mblunt/DETECTS2020/Pictures/0001-3077525328.png

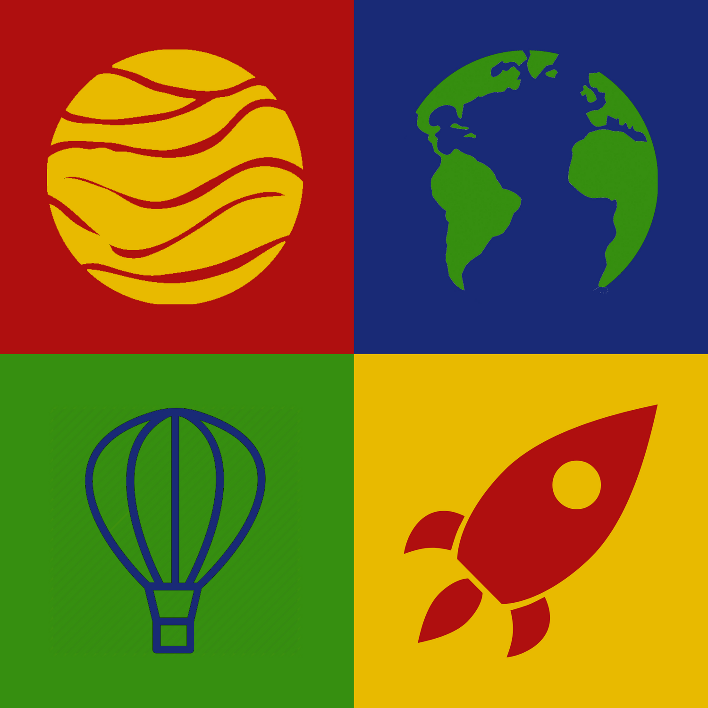
Pictures/0001-3077525328.png
