mblunt/DETECTS2020/Pictures/20191219_141400.jpg

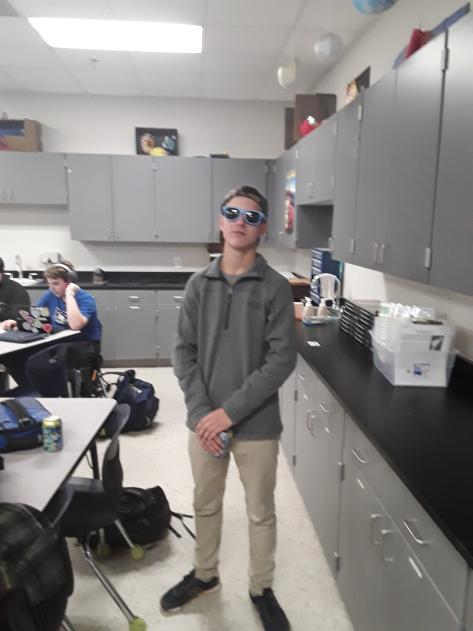
Pictures/20191219_141400.jpg
