mblunt/DETECTS2020/Pictures/After burn.jpg

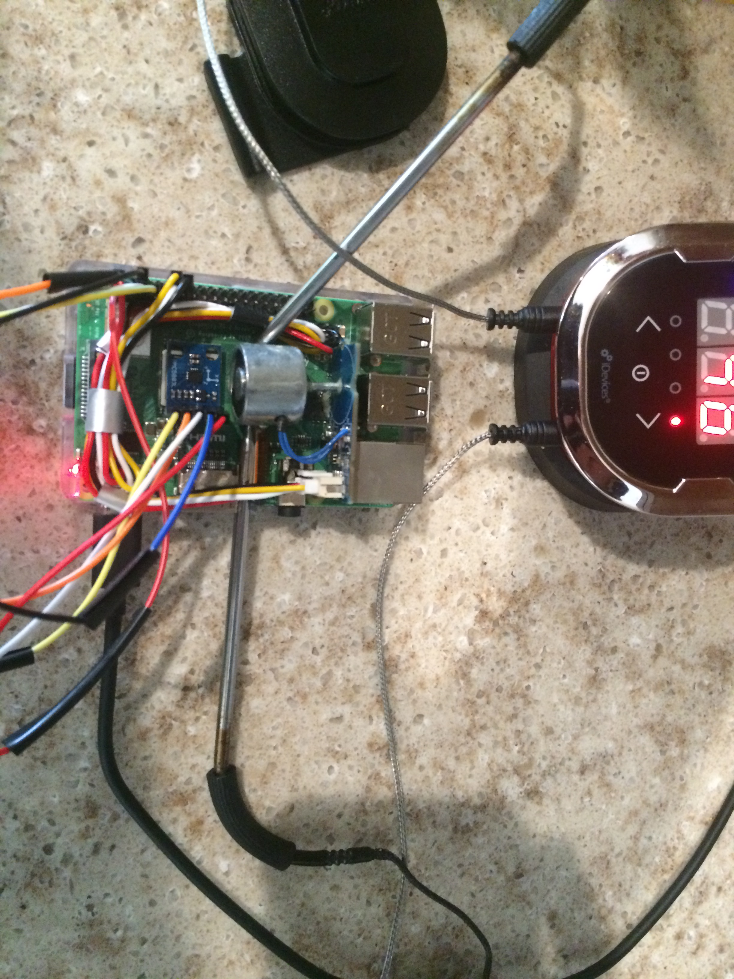
Pictures/After burn.jpg
