mblunt/DETECTS2020/Pictures/Burning PM.jpg

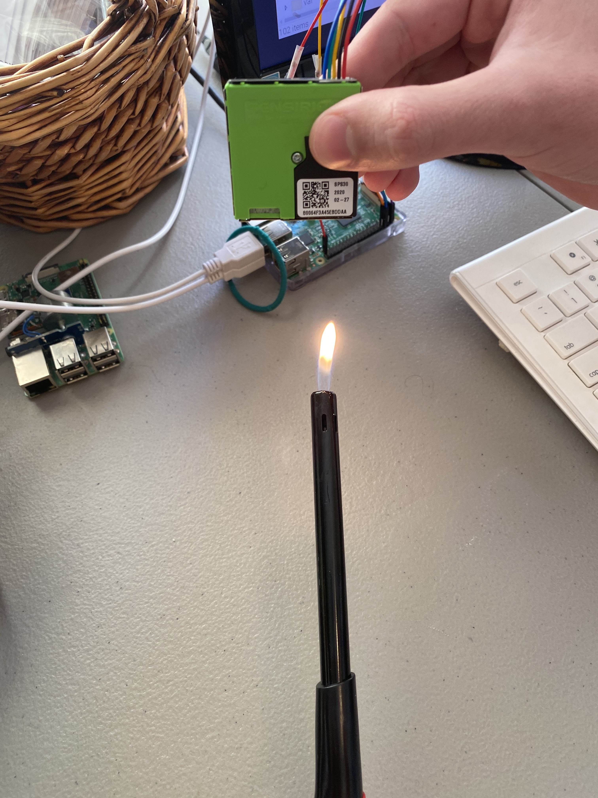
Pictures/Burning PM.jpg
