mblunt/DETECTS2020/Pictures/CAD_model.PNG

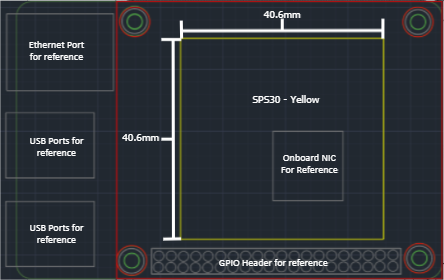
Pictures/CAD_model.PNG
