mblunt/DETECTS2020/Pictures/consistency_picture.PNG

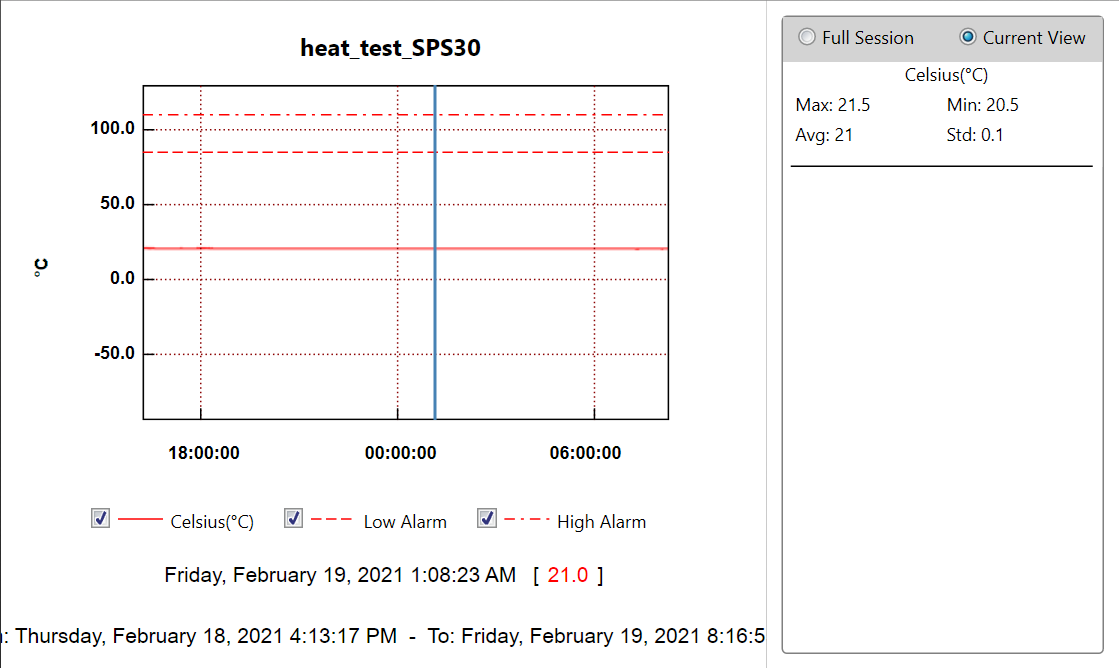
Pictures/consistency_picture.PNG
