mblunt/DETECTS2020/Pictures/datapacket.png

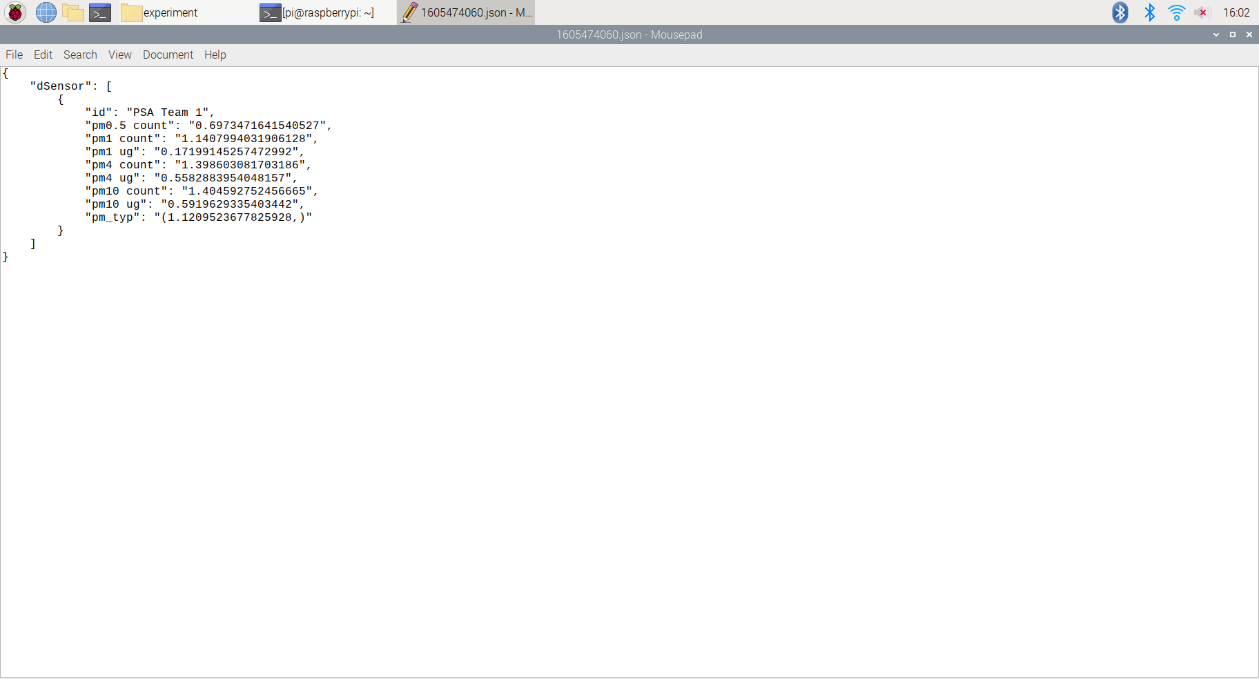
Pictures/datapacket.png
