mblunt/DETECTS2020/Pictures/datarate.png

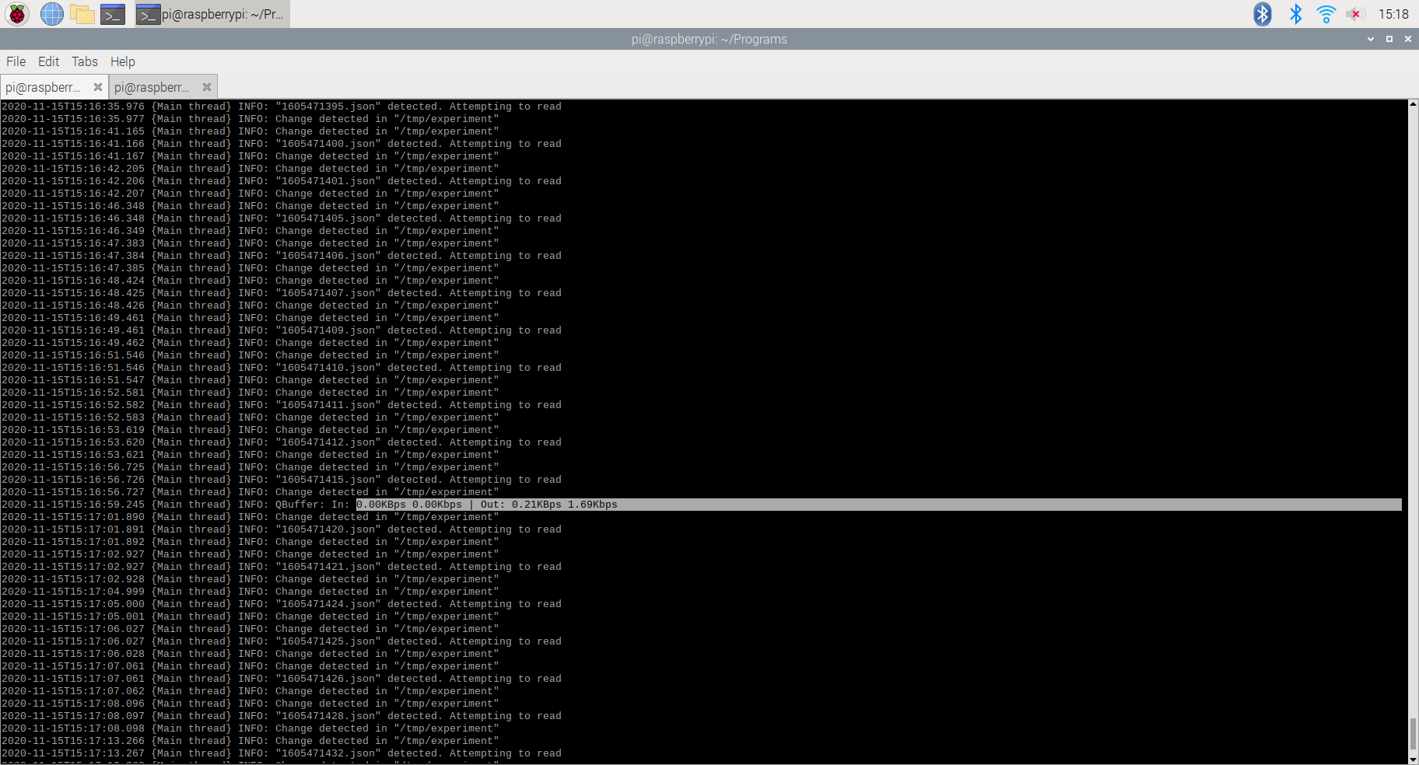
Pictures/datarate.png
