mblunt/DETECTS2020/Pictures/File_000(1).jpeg

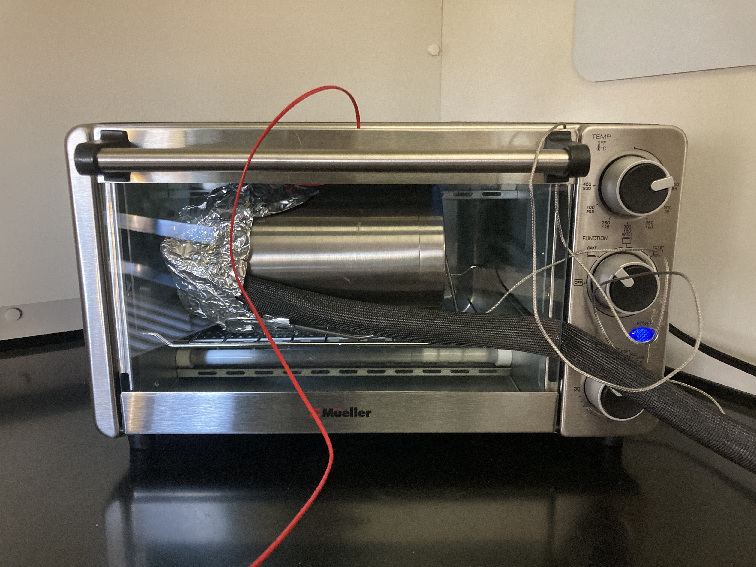
Pictures/File_000(1).jpeg
