mblunt/DETECTS2020/Pictures/File_000(5).jpeg

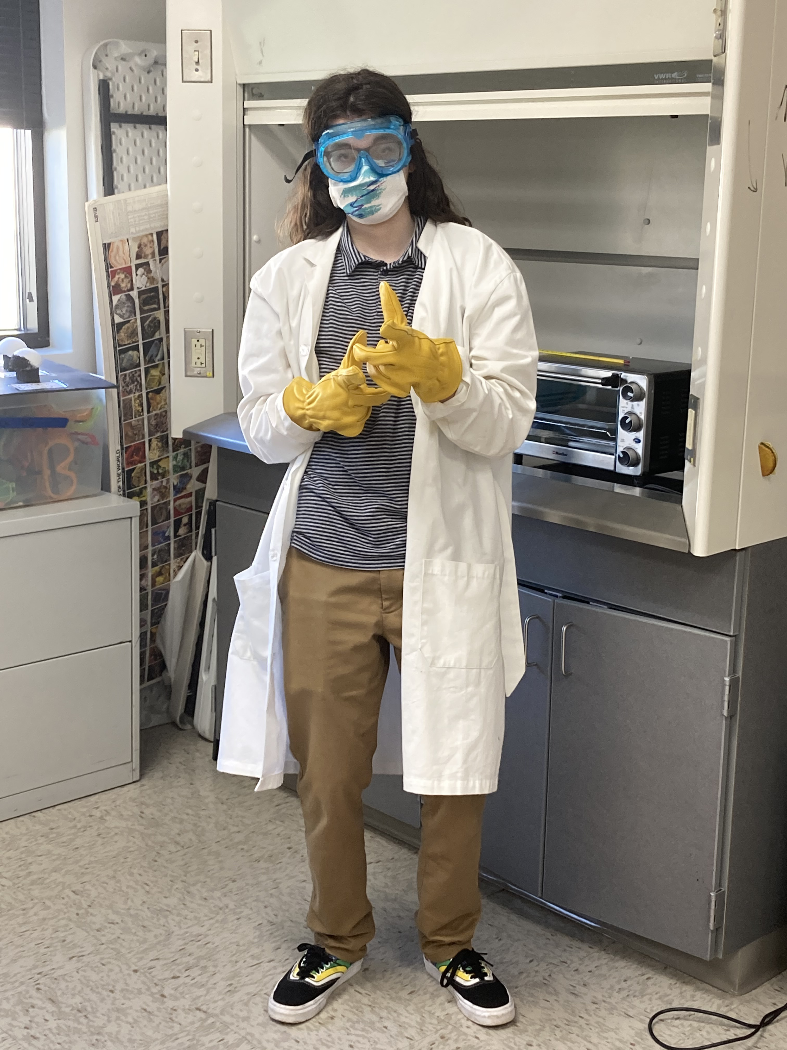
Pictures/File_000(5).jpeg
