mblunt/DETECTS2020/Pictures/File_000(6).jpeg

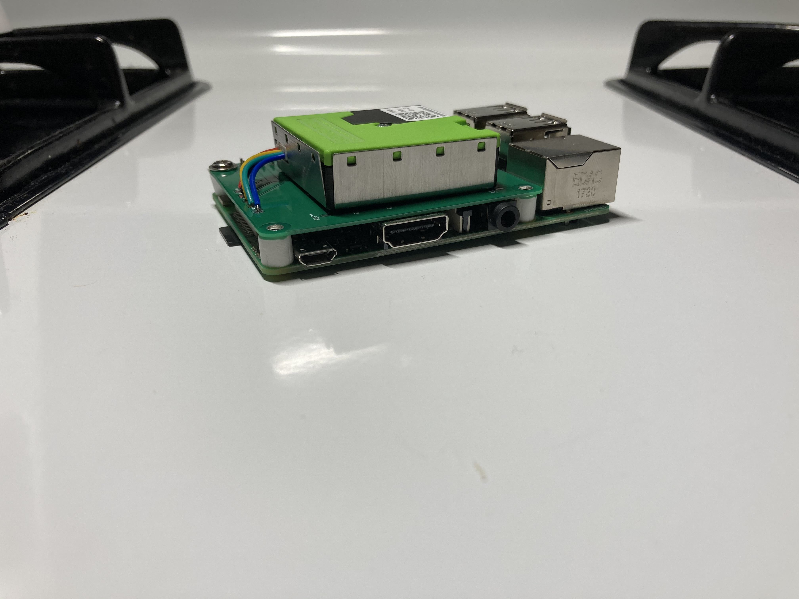
Pictures/File_000(6).jpeg
