mblunt/DETECTS2020/Pictures/File_000(7).jpeg

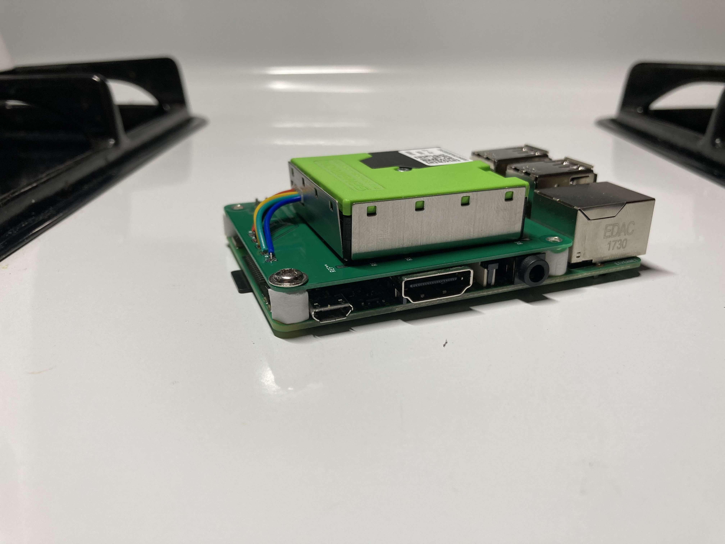
Pictures/File_000(7).jpeg
