mblunt/DETECTS2020/Pictures/File_000(8).jpeg

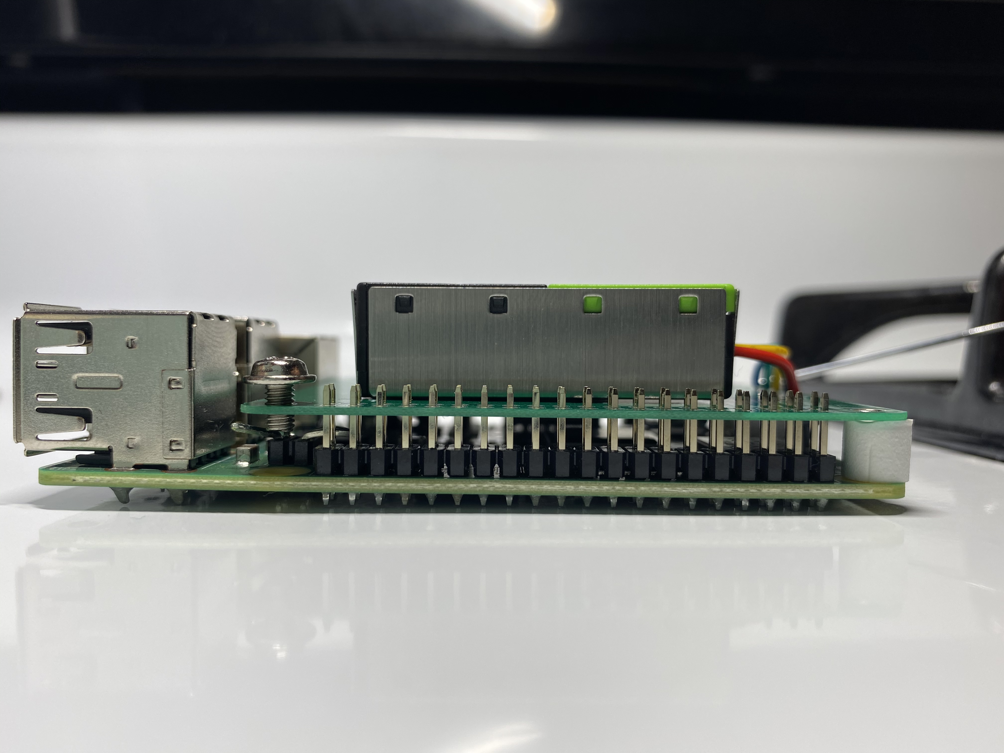
Pictures/File_000(8).jpeg
