mblunt/DETECTS2020/Pictures/File_000(9).jpeg

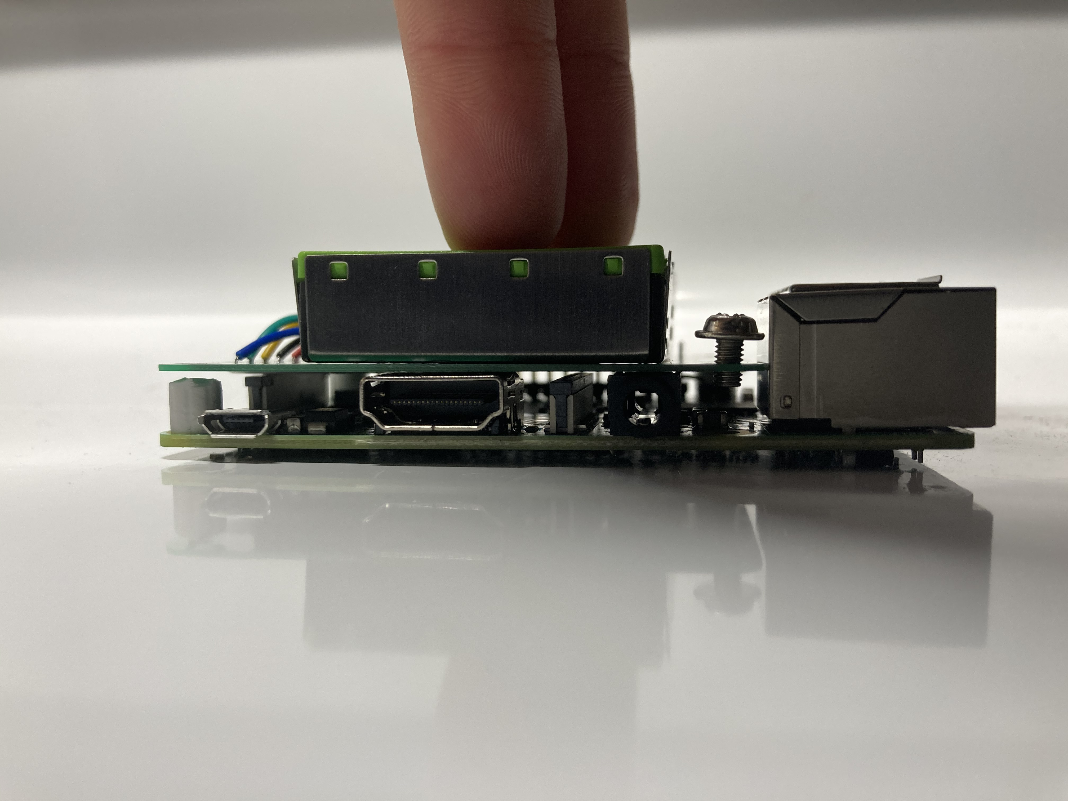
Pictures/File_000(9).jpeg
