mblunt/DETECTS2020/Pictures/File_000(10).jpeg

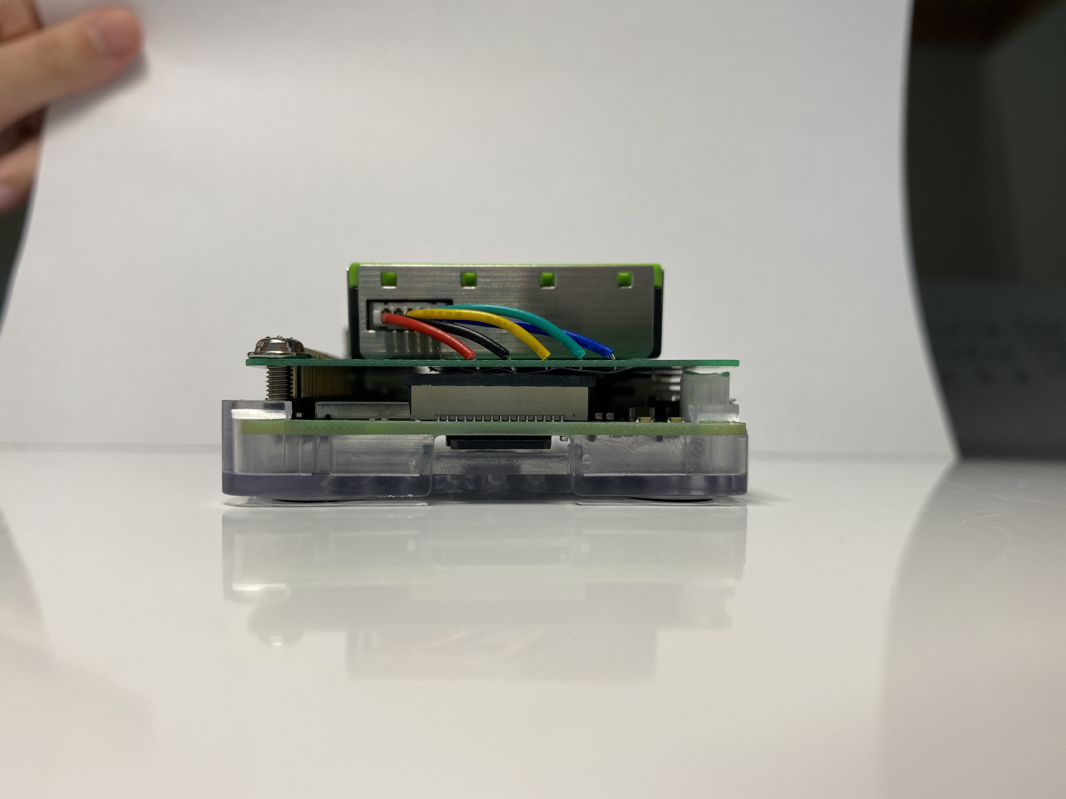
Pictures/File_000(10).jpeg
