mblunt/DETECTS2020/Pictures/File_000.jpeg

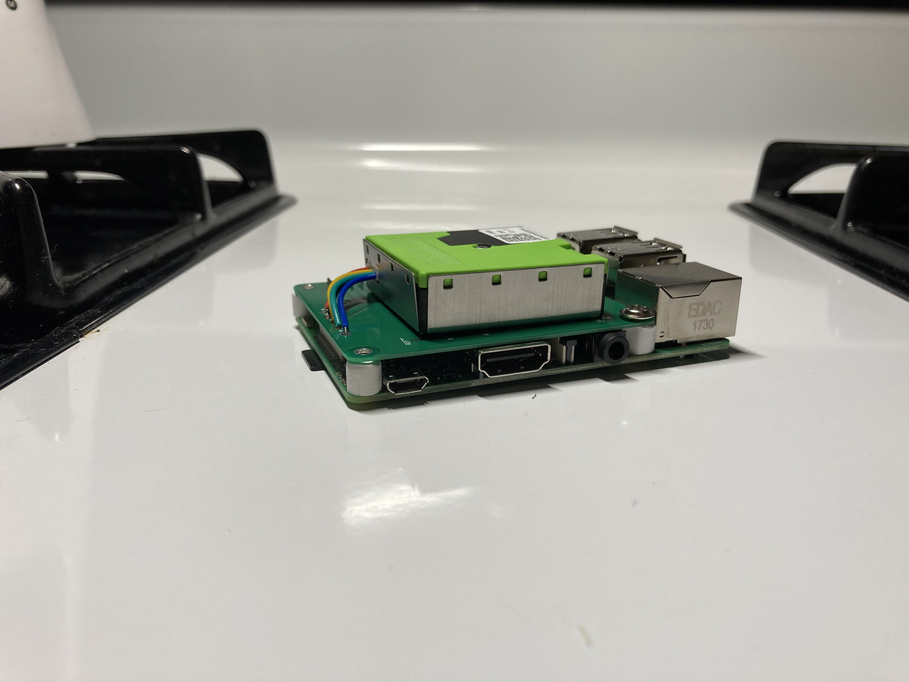
Pictures/File_000.jpeg
