mblunt/DETECTS2020/Pictures/File_001(2).jpeg

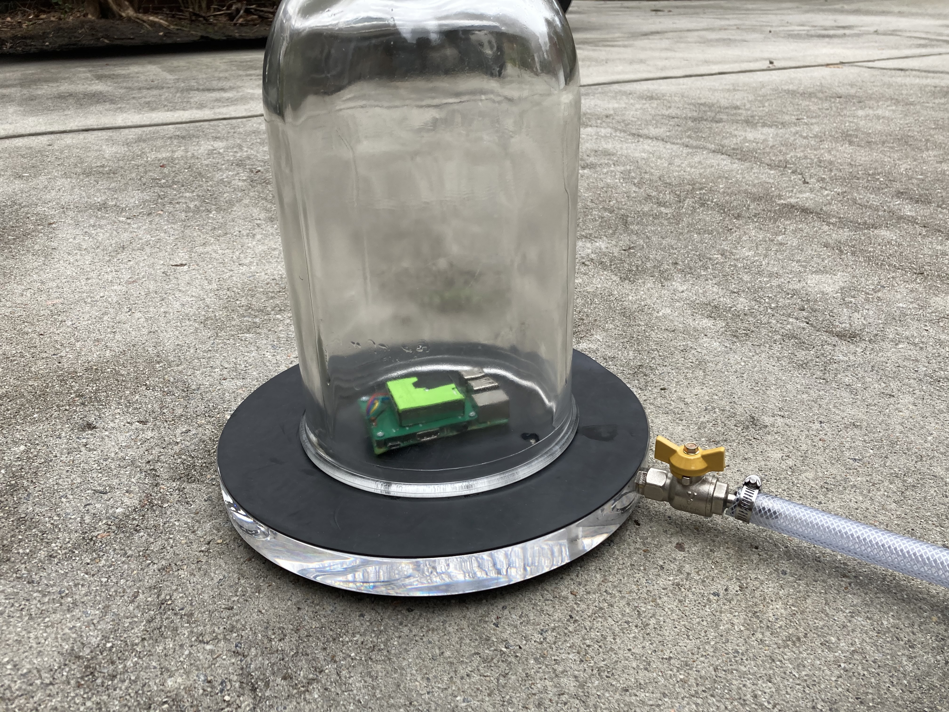
Pictures/File_001(2).jpeg
