mblunt/DETECTS2020/Pictures/File_001(3).jpeg

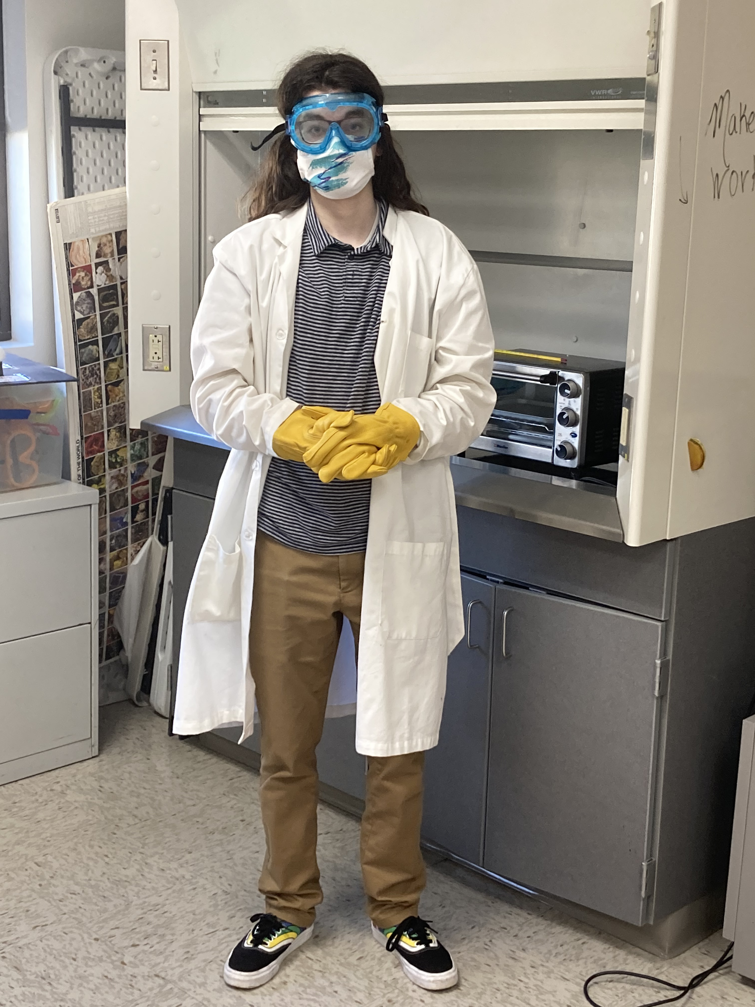
Pictures/File_001(3).jpeg
