mblunt/DETECTS2020/Pictures/File_001(6).jpeg

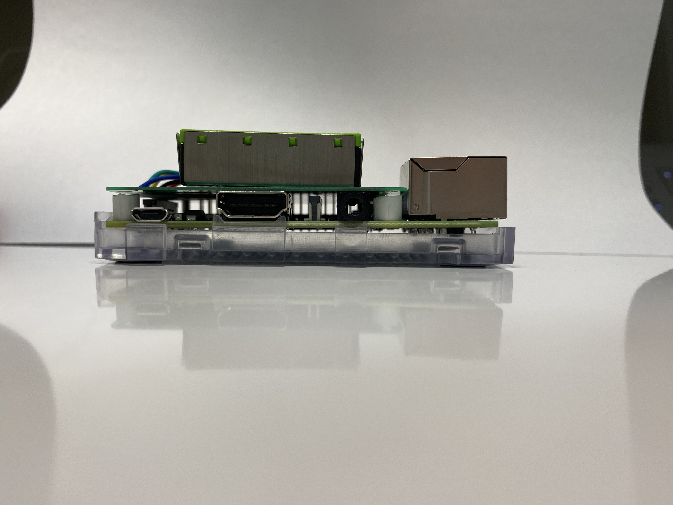
Pictures/File_001(6).jpeg
