mblunt/DETECTS2020/Pictures/File_001.jpeg

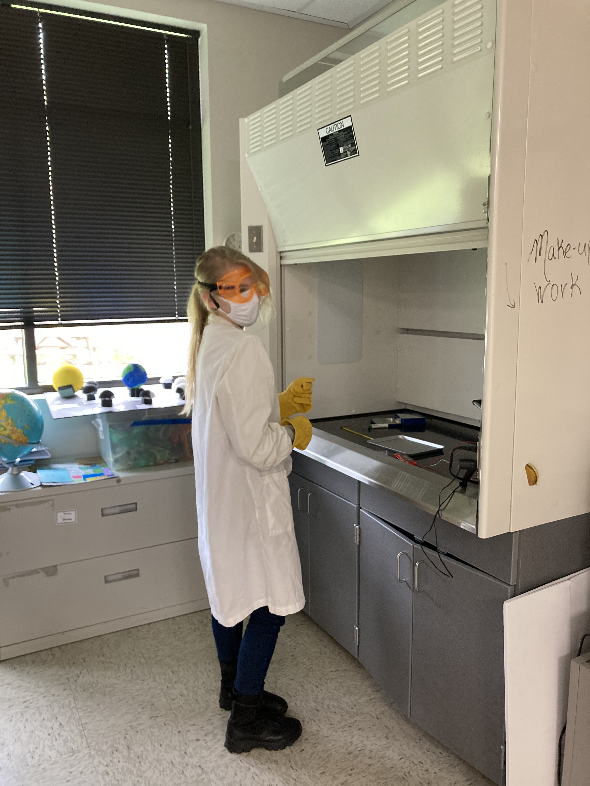
Pictures/File_001.jpeg
