mblunt/DETECTS2020/Pictures/File_002(1).jpeg

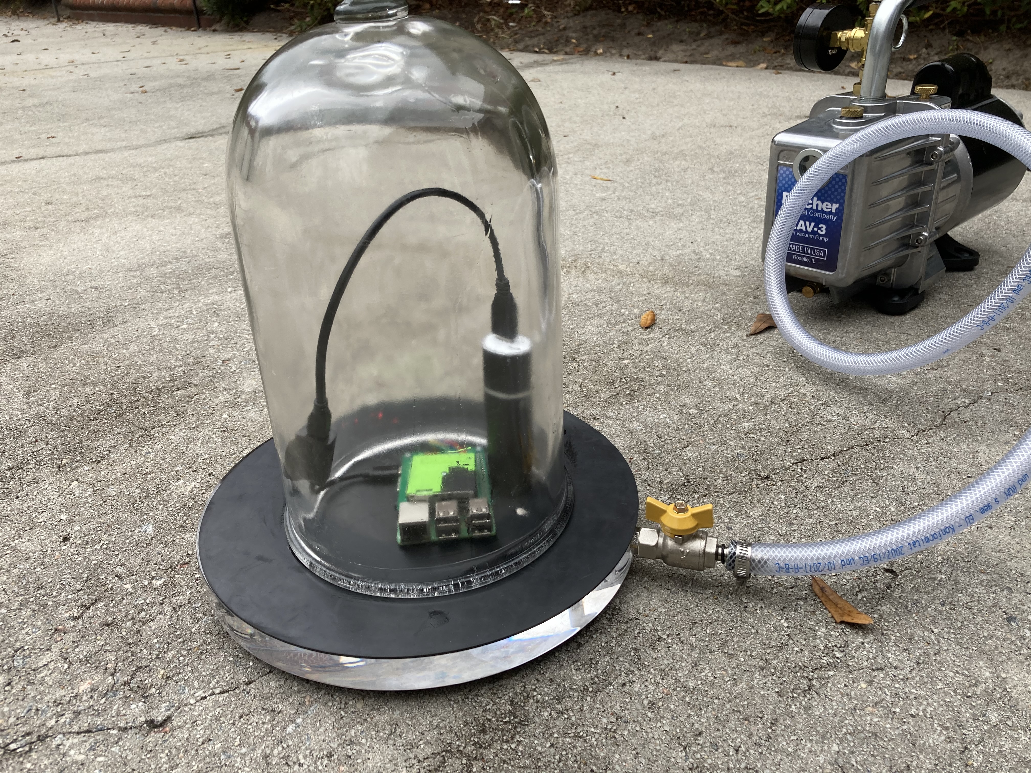
Pictures/File_002(1).jpeg
