mblunt/DETECTS2020/Pictures/File_002(2).jpeg

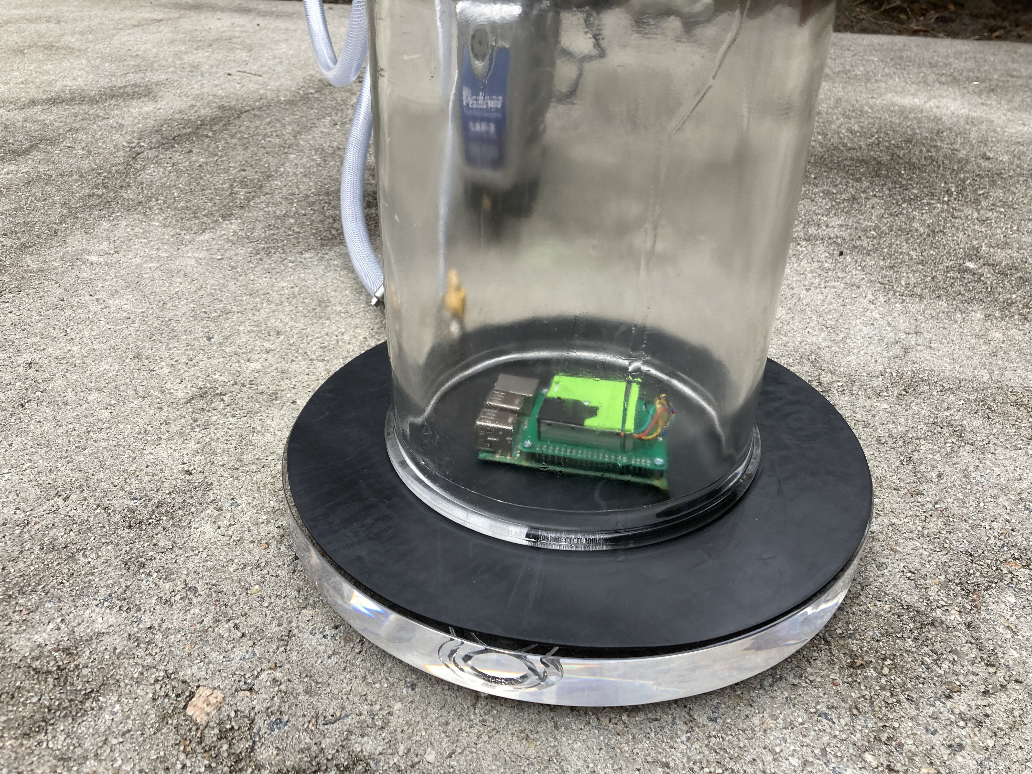
Pictures/File_002(2).jpeg
