mblunt/DETECTS2020/Pictures/File_002(3).jpeg

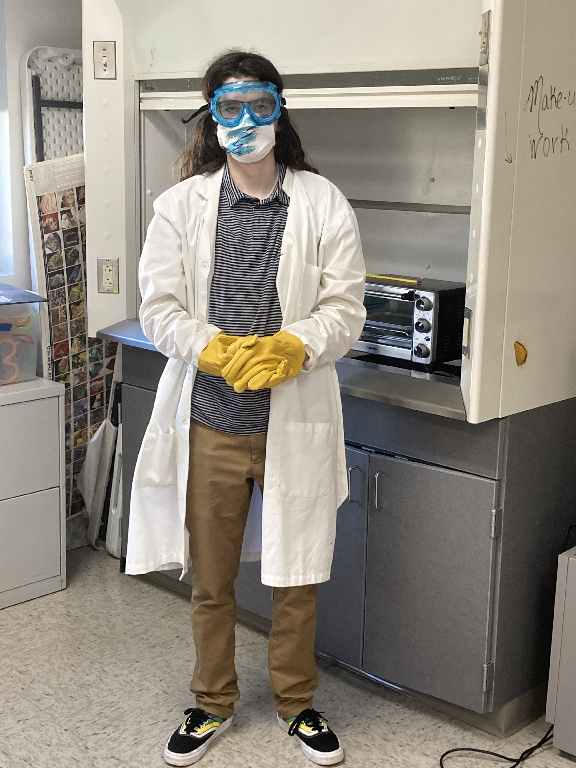
Pictures/File_002(3).jpeg
