mblunt/DETECTS2020/Pictures/File_002(4).jpeg

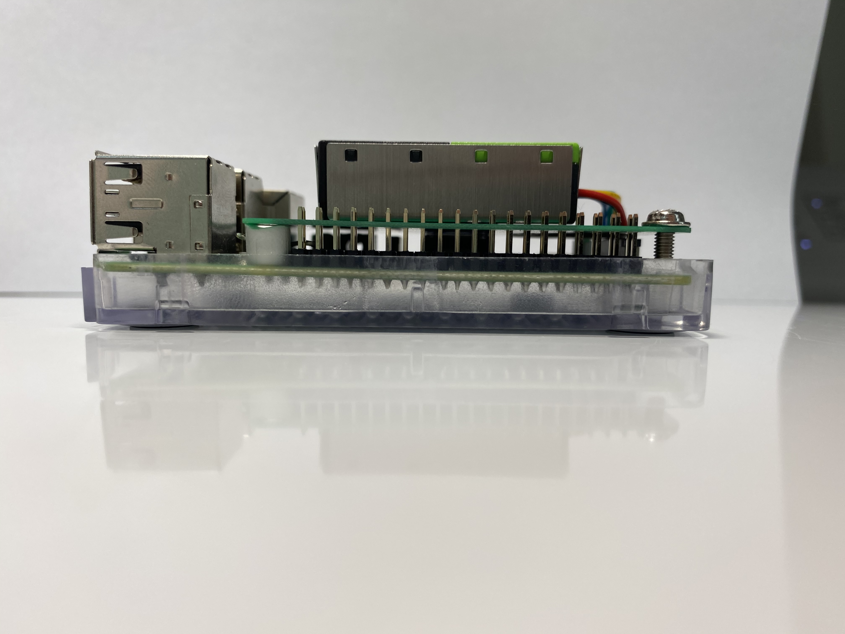
Pictures/File_002(4).jpeg
