mblunt/DETECTS2020/Pictures/File_002.jpeg

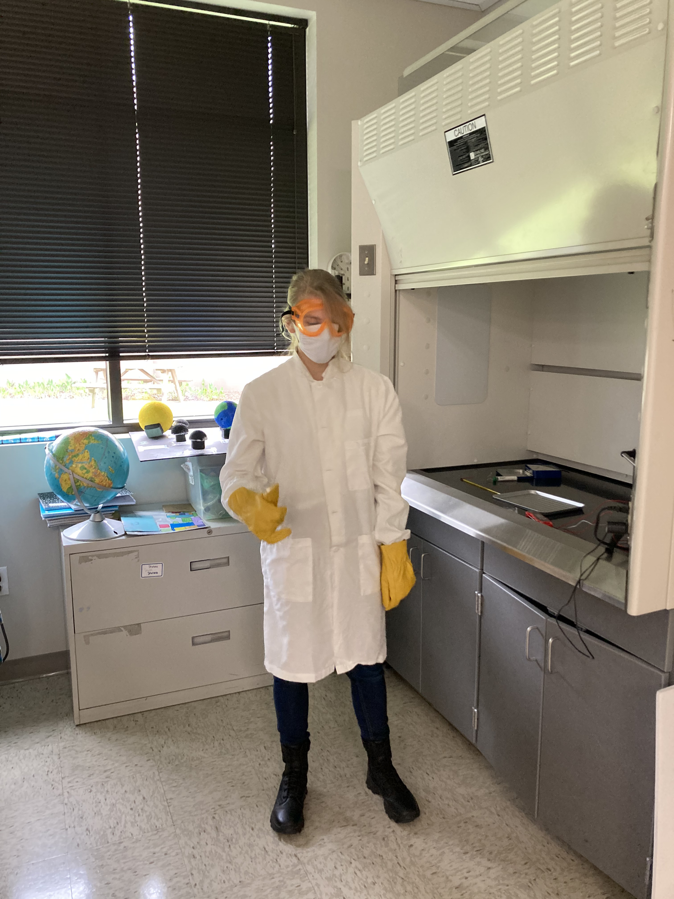
Pictures/File_002.jpeg
