mblunt/DETECTS2020/Pictures/File_003(1).jpeg

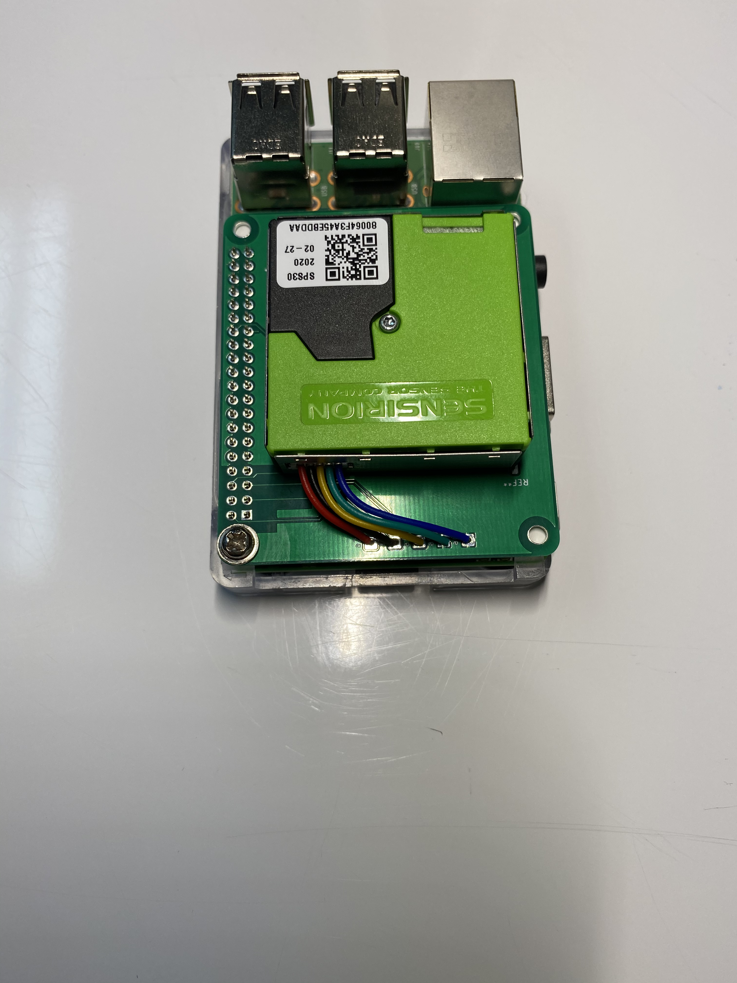
Pictures/File_003(1).jpeg
