mblunt/DETECTS2020/Pictures/File_003(2).jpeg

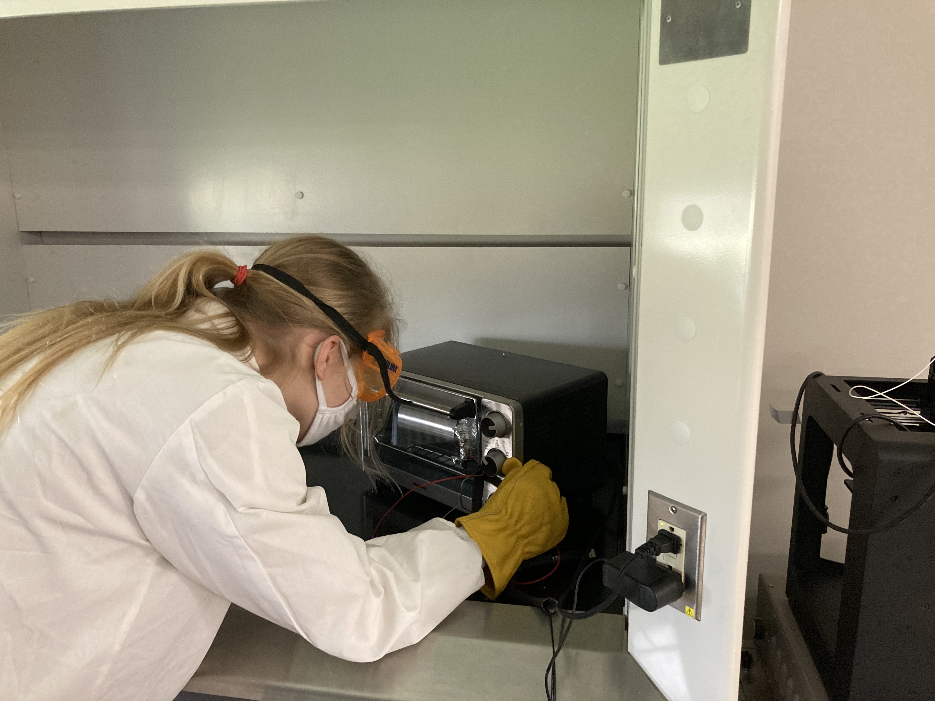
Pictures/File_003(2).jpeg
