mblunt/DETECTS2020/Pictures/File_003(3).jpeg

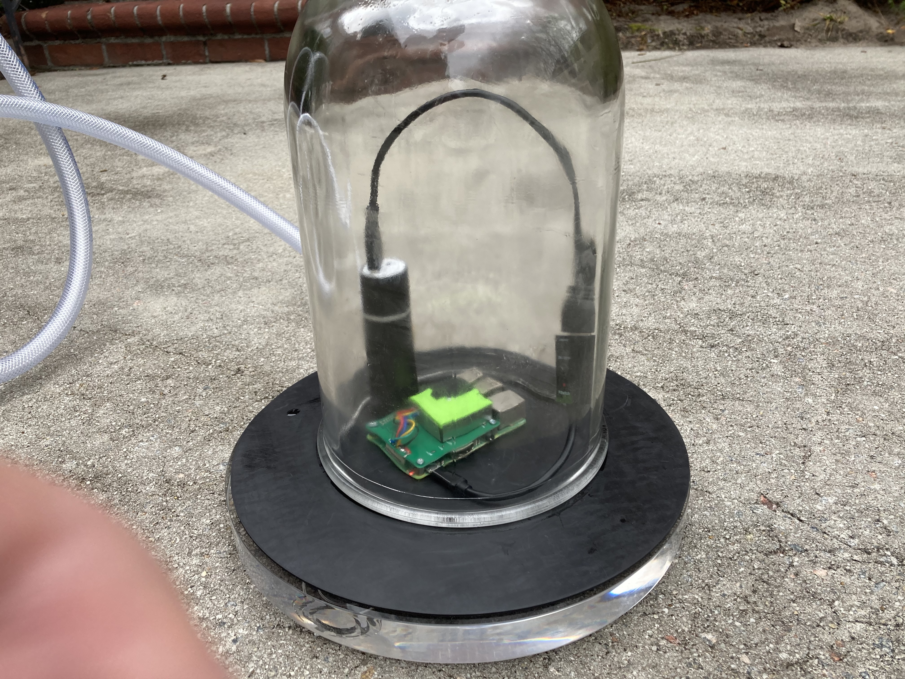
Pictures/File_003(3).jpeg
