mblunt/DETECTS2020/Pictures/File_003.jpeg

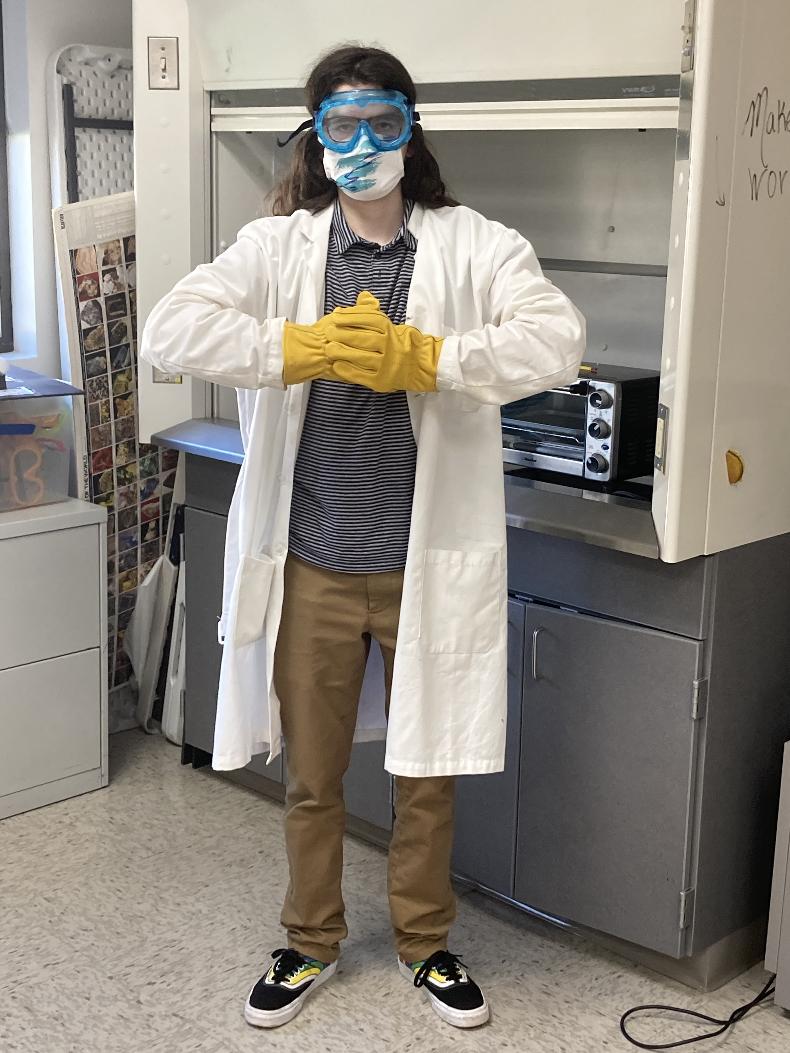
Pictures/File_003.jpeg
