mblunt/DETECTS2020/Pictures/File_004(3).jpeg

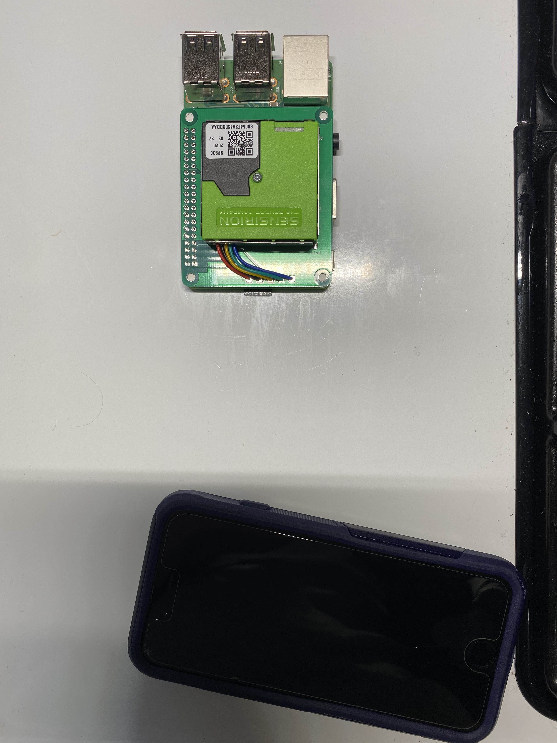
Pictures/File_004(3).jpeg
