mblunt/DETECTS2020/Pictures/File_004.jpeg

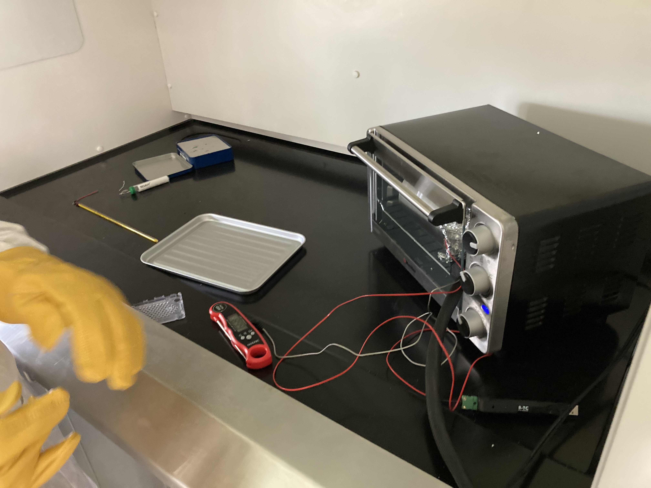
Pictures/File_004.jpeg
