mblunt/DETECTS2020/Pictures/File_005.jpeg

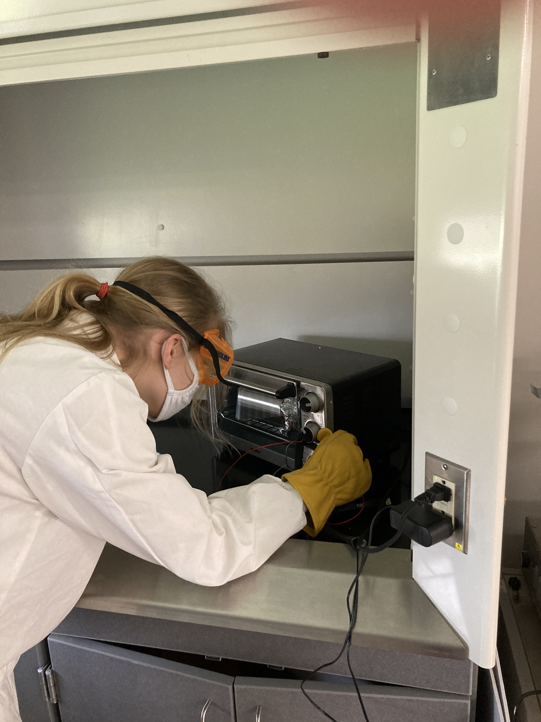
Pictures/File_005.jpeg
