mblunt/DETECTS2020/Pictures/File_007.jpeg

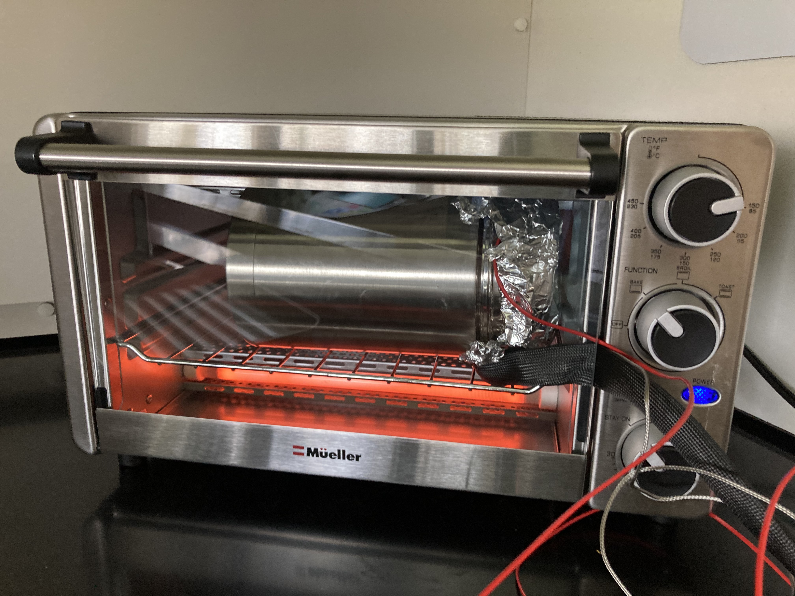
Pictures/File_007.jpeg
