mblunt/DETECTS2020/Pictures/File_008.jpeg

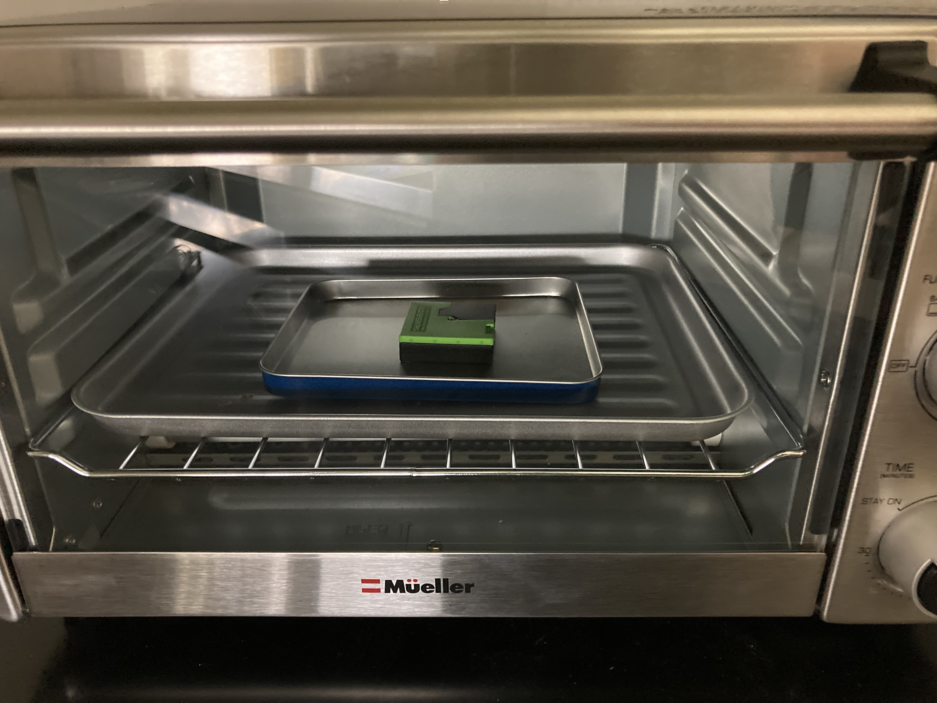
Pictures/File_008.jpeg
