mblunt/DETECTS2020/Pictures/File_009.jpeg

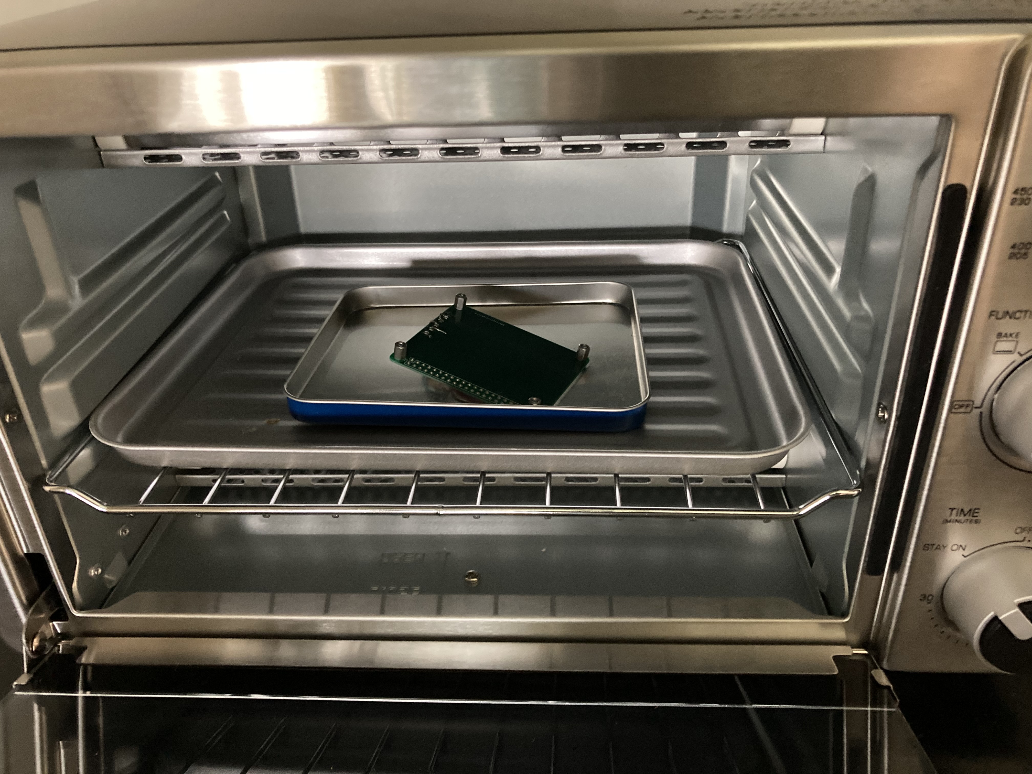
Pictures/File_009.jpeg
