mblunt/DETECTS2020/Pictures/File_010.jpeg

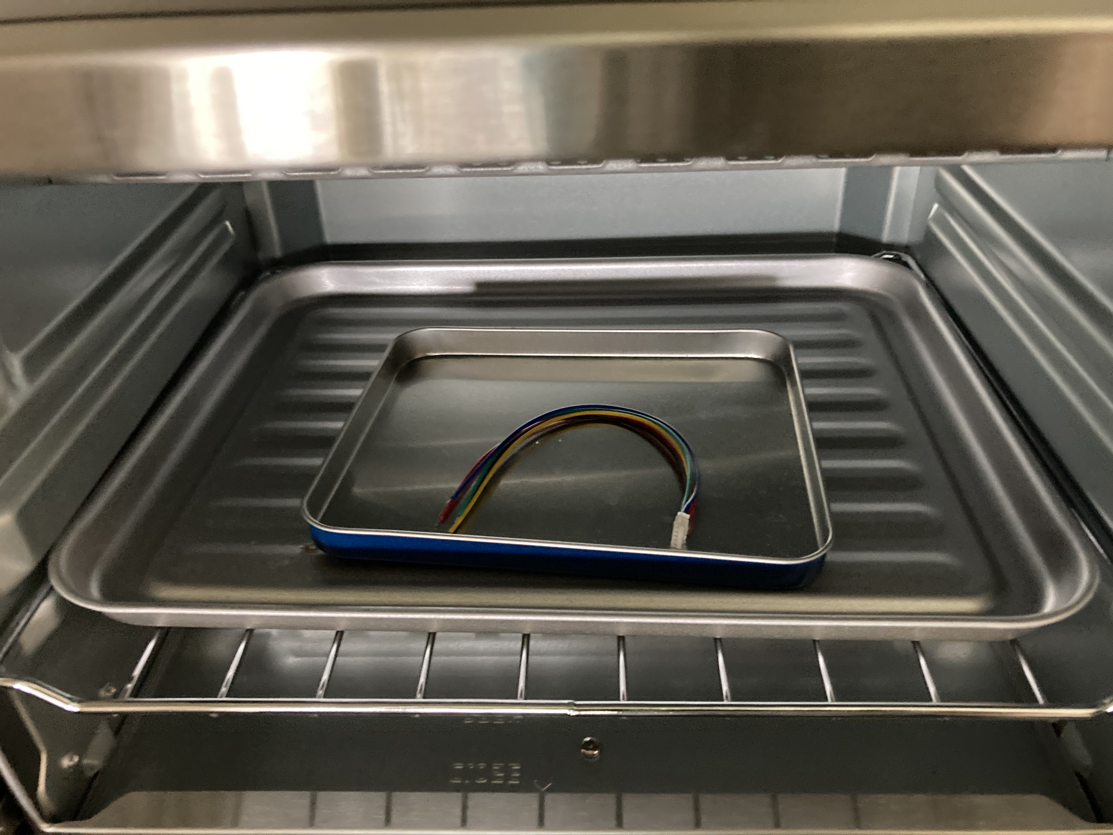
Pictures/File_010.jpeg
