mblunt/DETECTS2020/Pictures/FinalPayload1.jpg

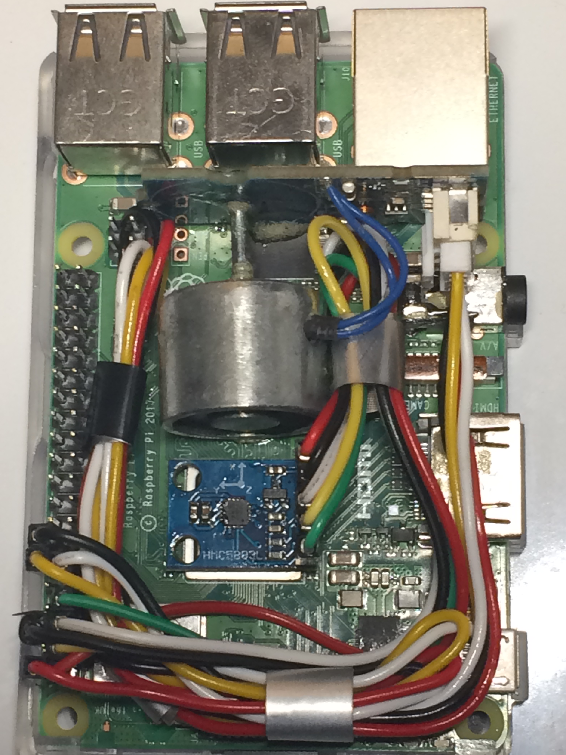
Pictures/FinalPayload1.jpg
