mblunt/DETECTS2020/Pictures/FinalPayload2.jpg

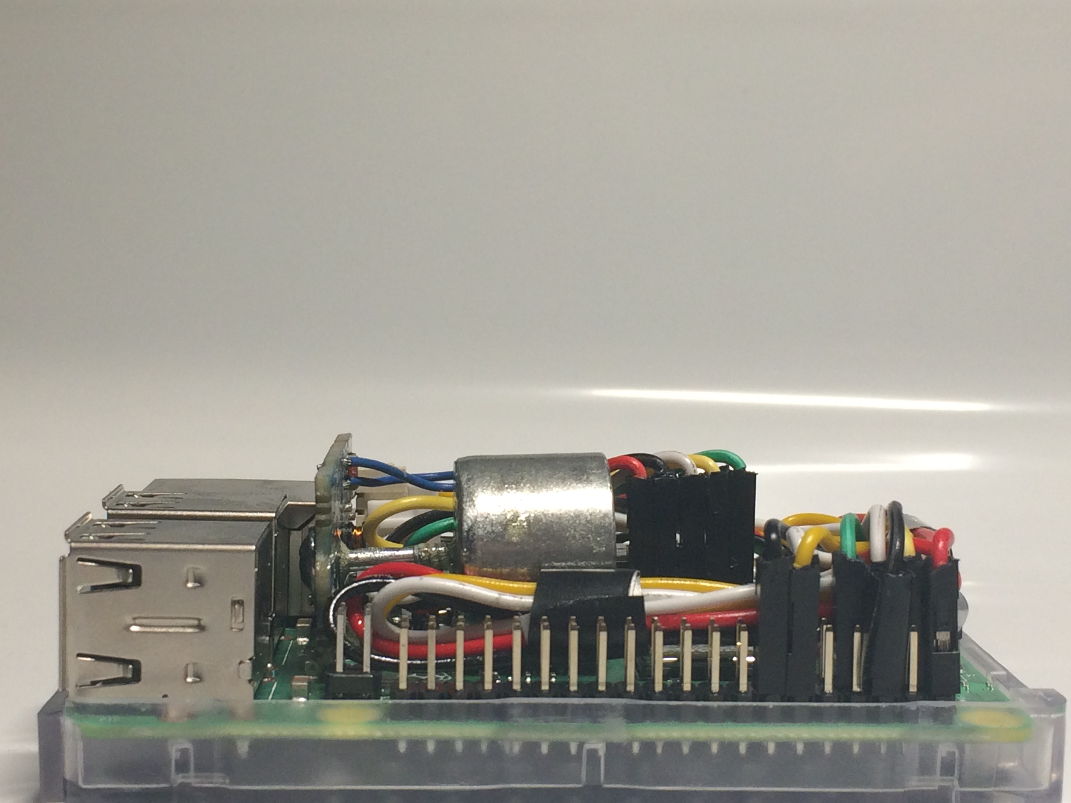
Pictures/FinalPayload2.jpg
