mblunt/DETECTS2020/Pictures/FinalPayload3.jpg

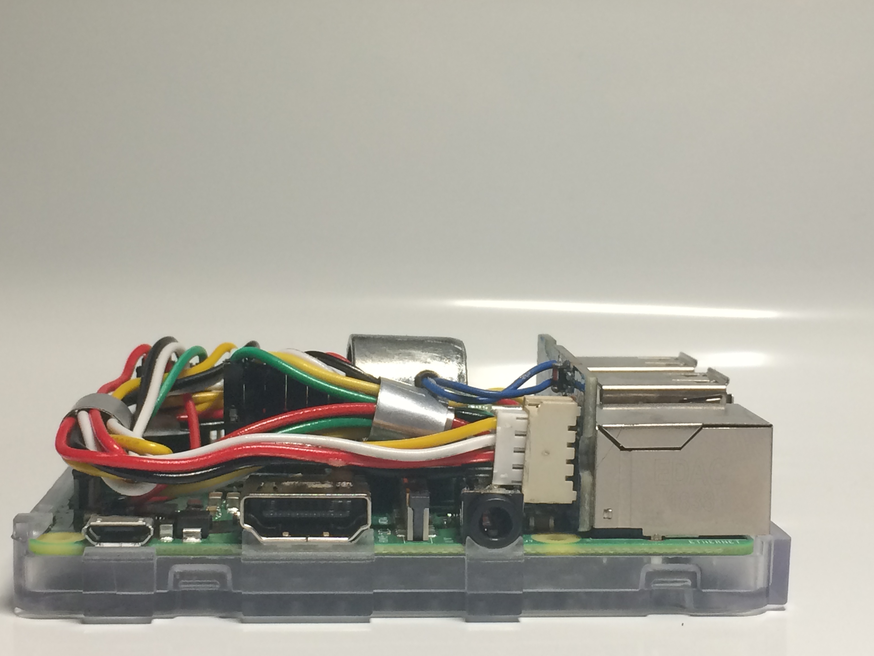
Pictures/FinalPayload3.jpg
