mblunt/DETECTS2020/Pictures/FinalPayload4.jpg

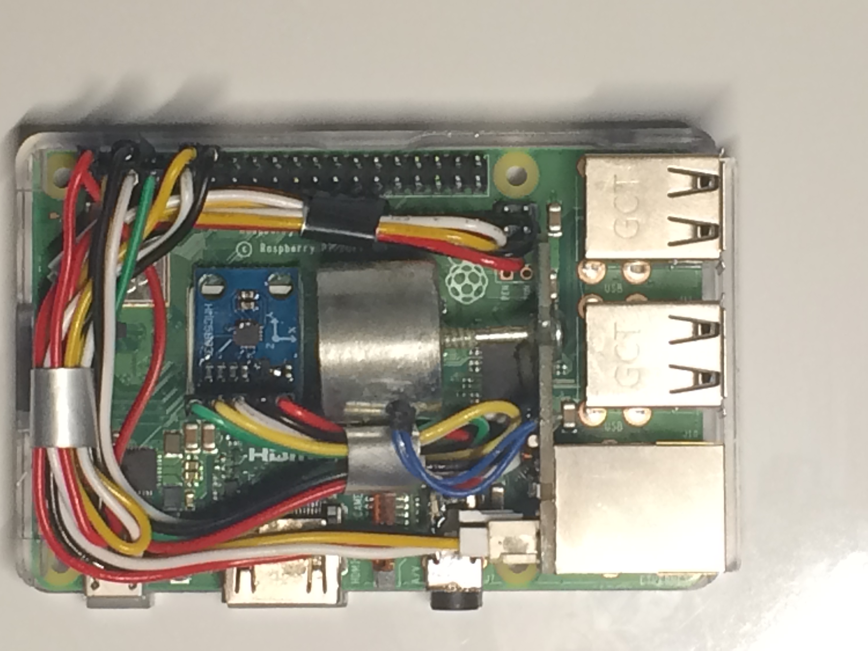
Pictures/FinalPayload4.jpg
