mblunt/DETECTS2020/Pictures/frontpage-underfold.jpg

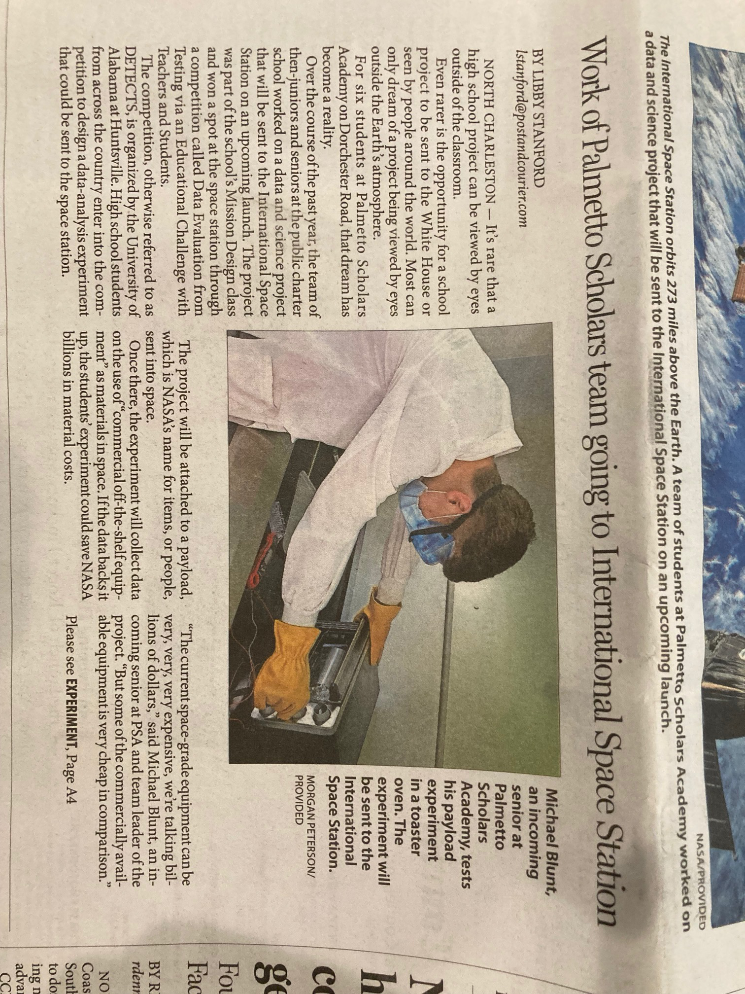
Pictures/frontpage-underfold.jpg
