mblunt/DETECTS2020/Pictures/HAT_blueprint.PNG

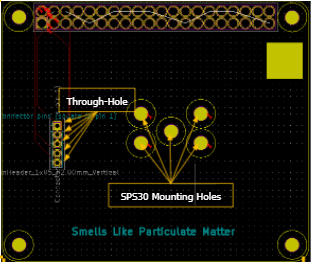
Pictures/HAT_blueprint.PNG
