mblunt/DETECTS2020/Pictures/heat_fullconfig_GRAPH.jpg

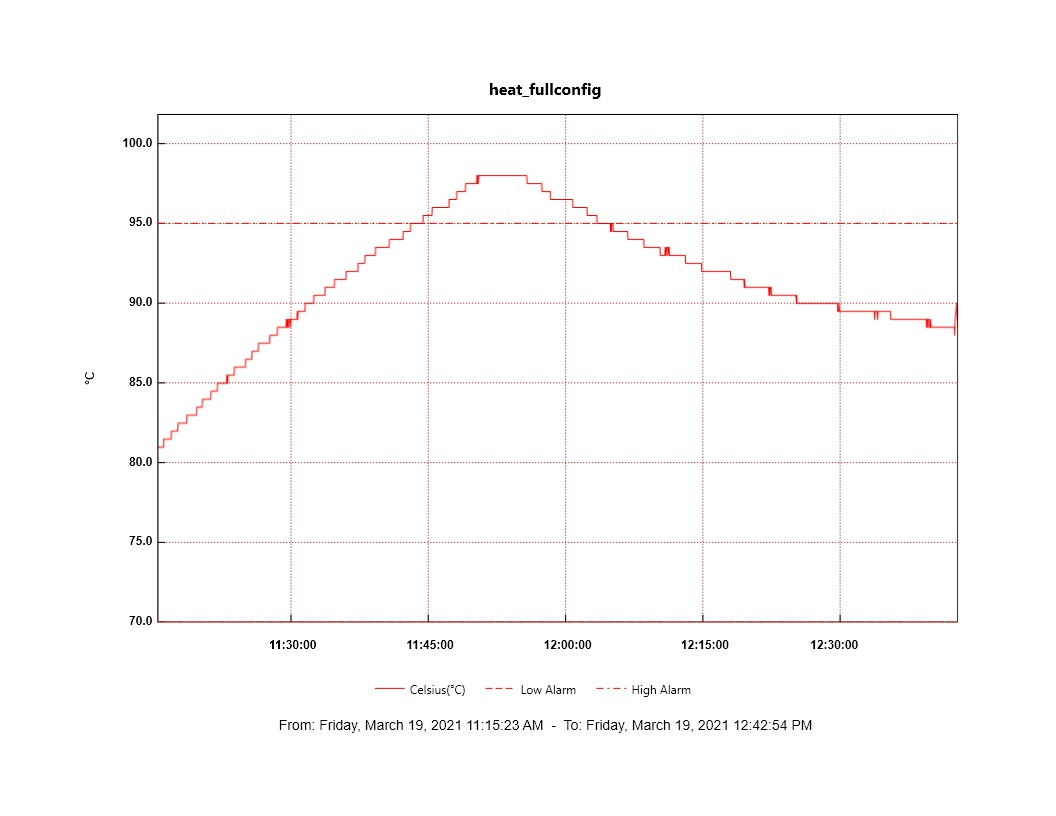
Pictures/heat_fullconfig_GRAPH.jpg
