mblunt/DETECTS2020/Pictures/IMG_3665.JPG

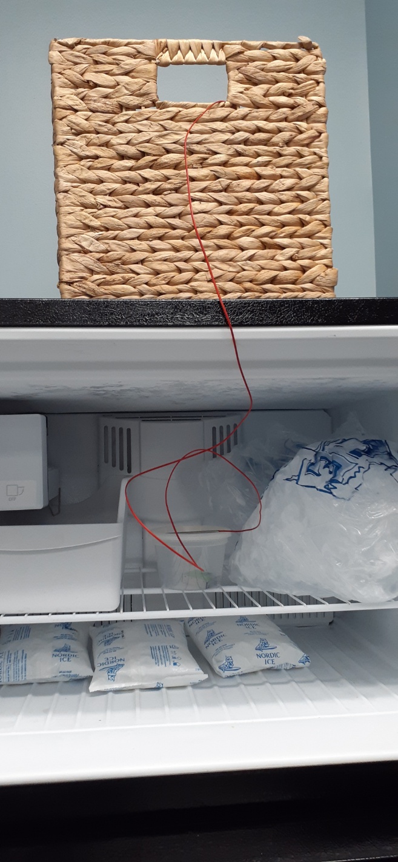
Pictures/IMG_3665.JPG
