mblunt/DETECTS2020/Pictures/IMG_3666.JPG

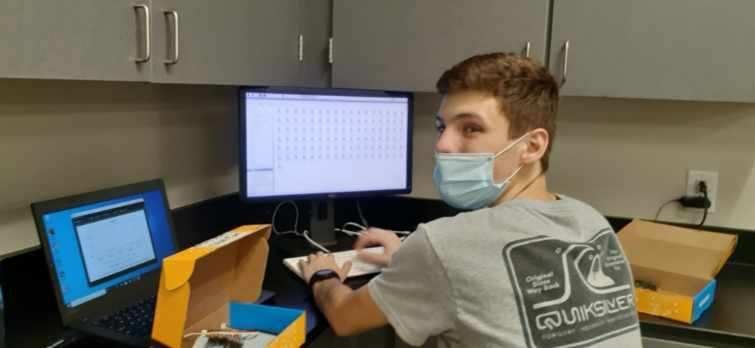
Pictures/IMG_3666.JPG
