mblunt/DETECTS2020/Pictures/IMG_3667.JPG

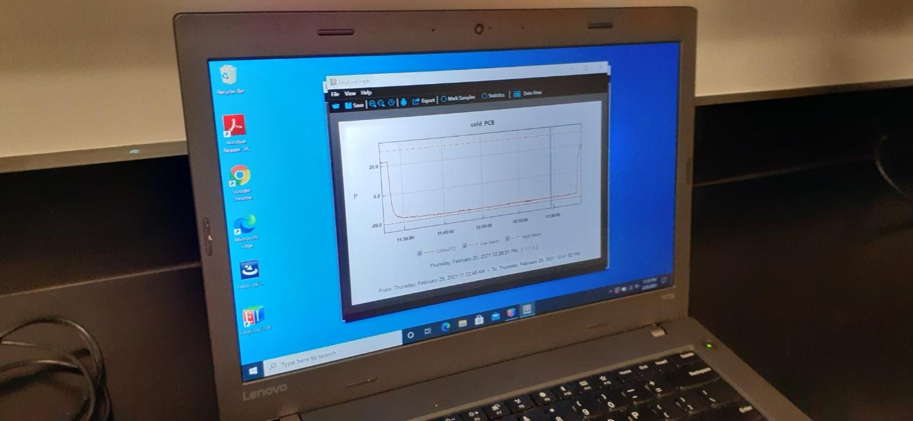
Pictures/IMG_3667.JPG
