mblunt/DETECTS2020/Pictures/IMG_3668.JPG

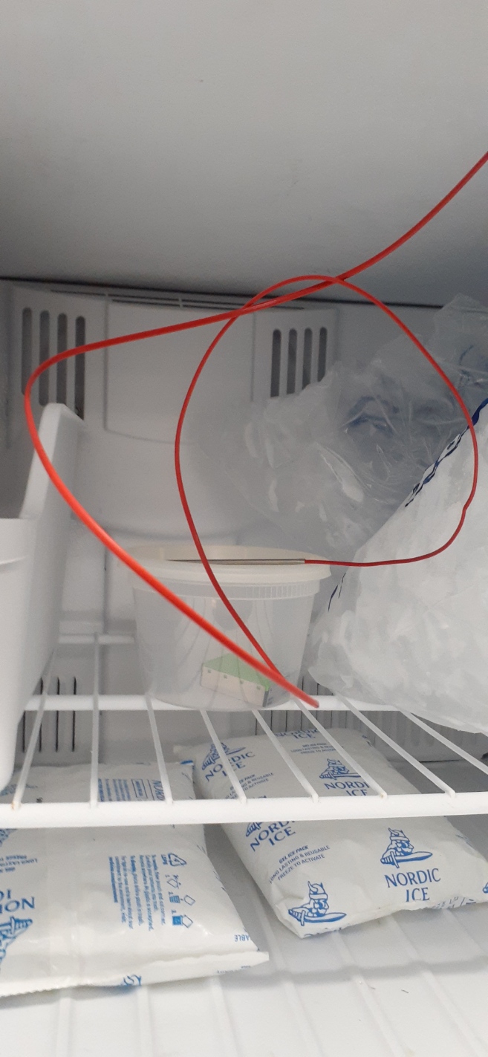
Pictures/IMG_3668.JPG
