mblunt/DETECTS2020/Pictures/IMG_3669.JPG

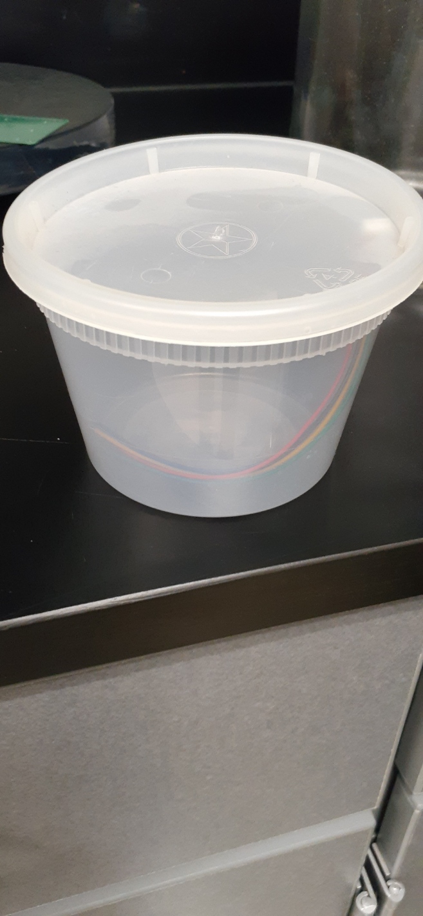
Pictures/IMG_3669.JPG
