mblunt/DETECTS2020/Pictures/IMG_3670.JPG

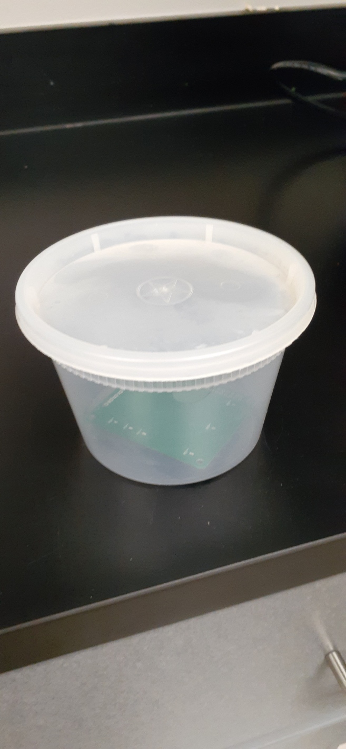
Pictures/IMG_3670.JPG
