mblunt/DETECTS2020/Pictures/IMG_3722.PNG

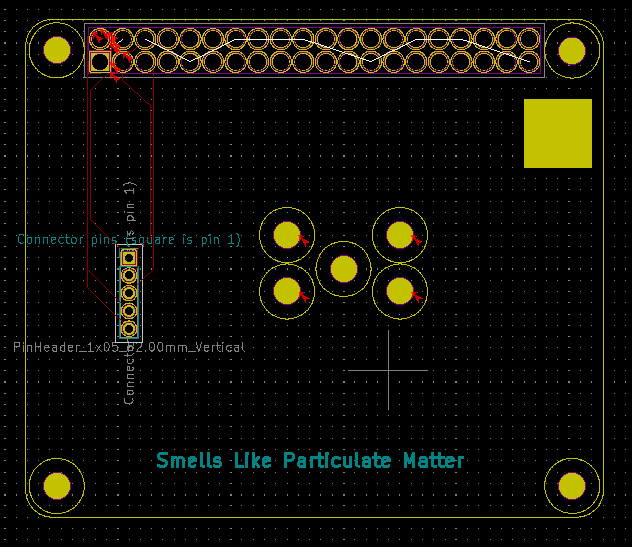
Pictures/IMG_3722.PNG
