mblunt/DETECTS2020/Pictures/IMG_6856.JPEG

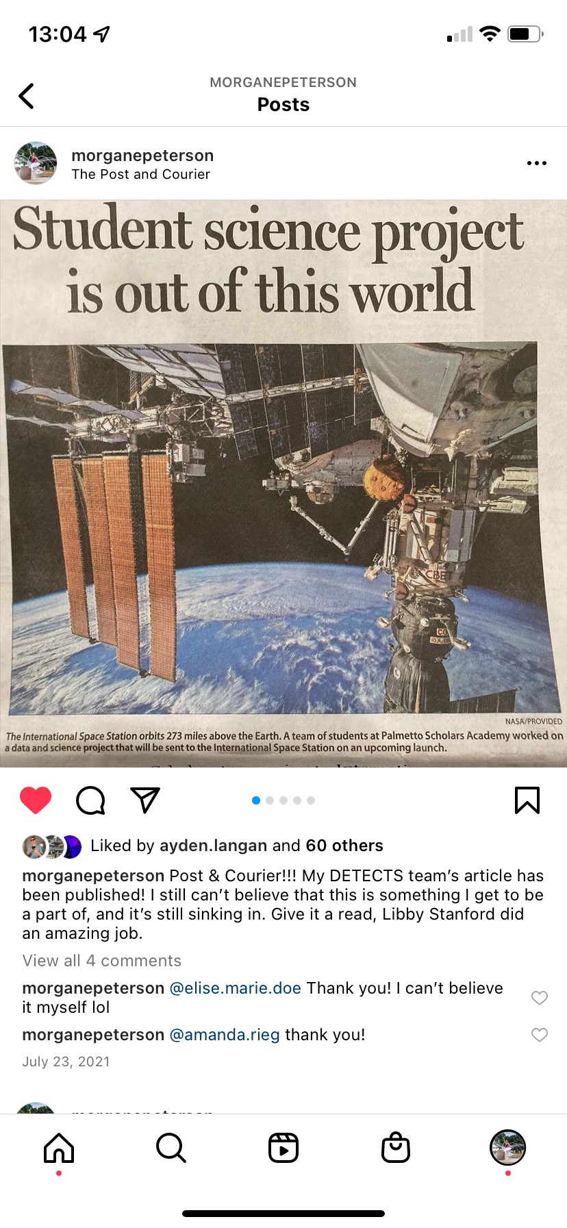
Pictures/IMG_6856.JPEG
