mblunt/DETECTS2020/Pictures/IMG_6857.JPEG

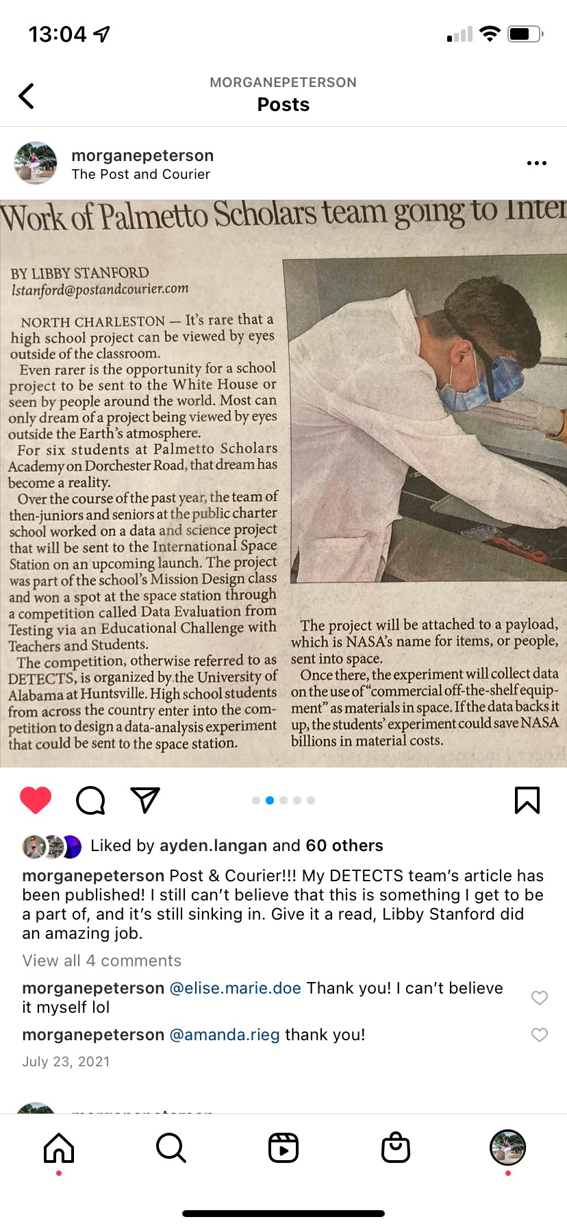
Pictures/IMG_6857.JPEG
