mblunt/DETECTS2020/Pictures/IMG_6858.JPEG

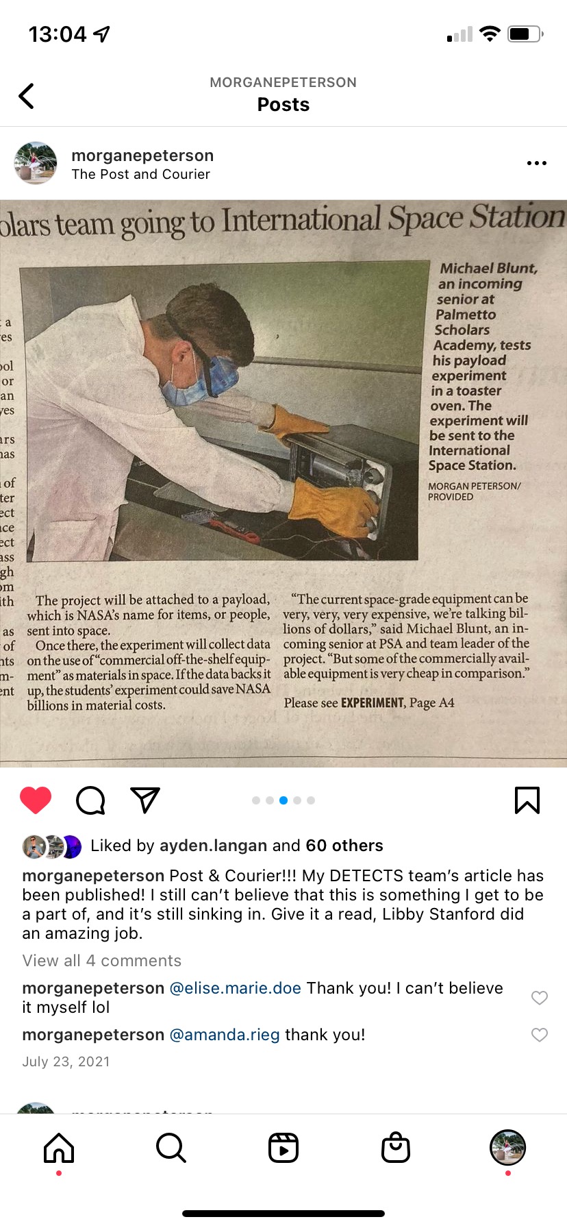
Pictures/IMG_6858.JPEG
