mblunt/DETECTS2020/Pictures/IMG_6859.JPEG

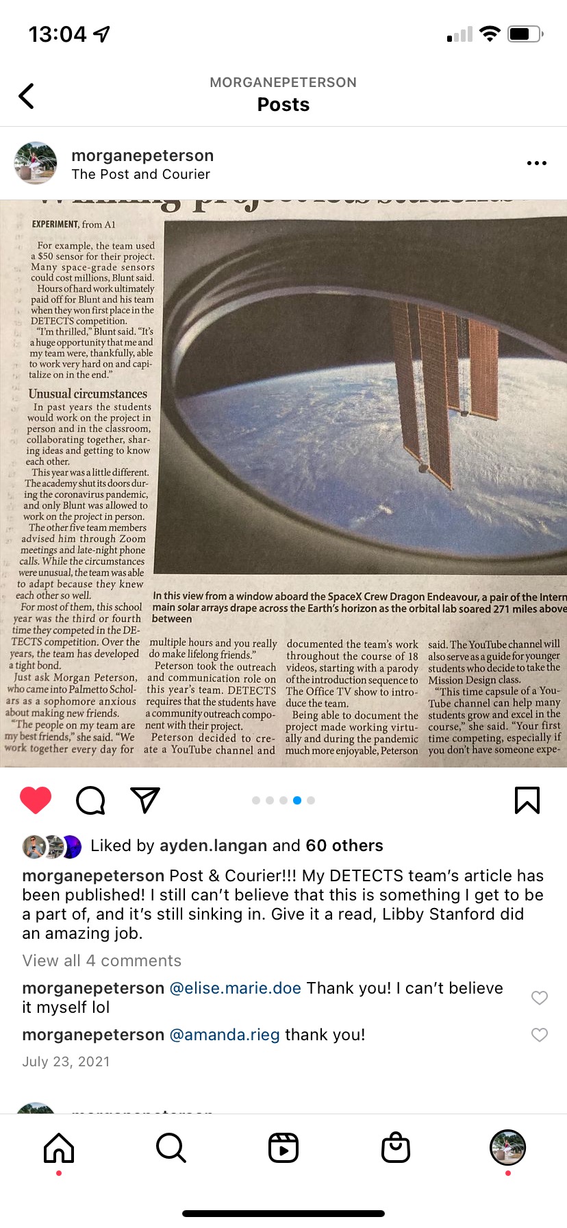
Pictures/IMG_6859.JPEG
