mblunt/DETECTS2020/Pictures/IMG_6860.JPEG

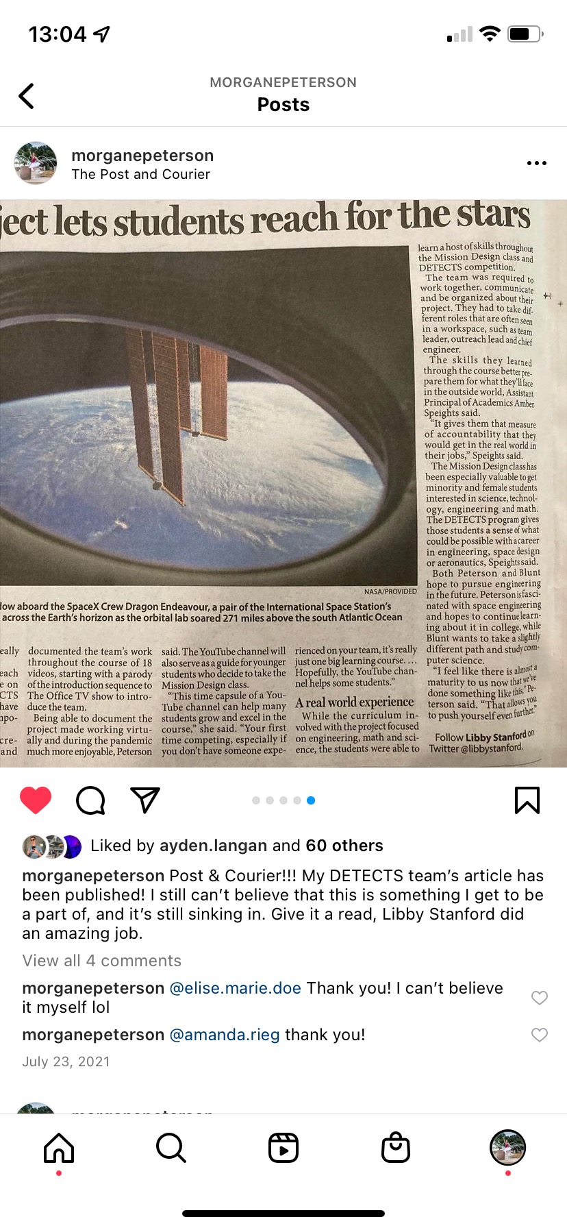
Pictures/IMG_6860.JPEG
