mblunt/DETECTS2020/Pictures/lighter_pm_count.png

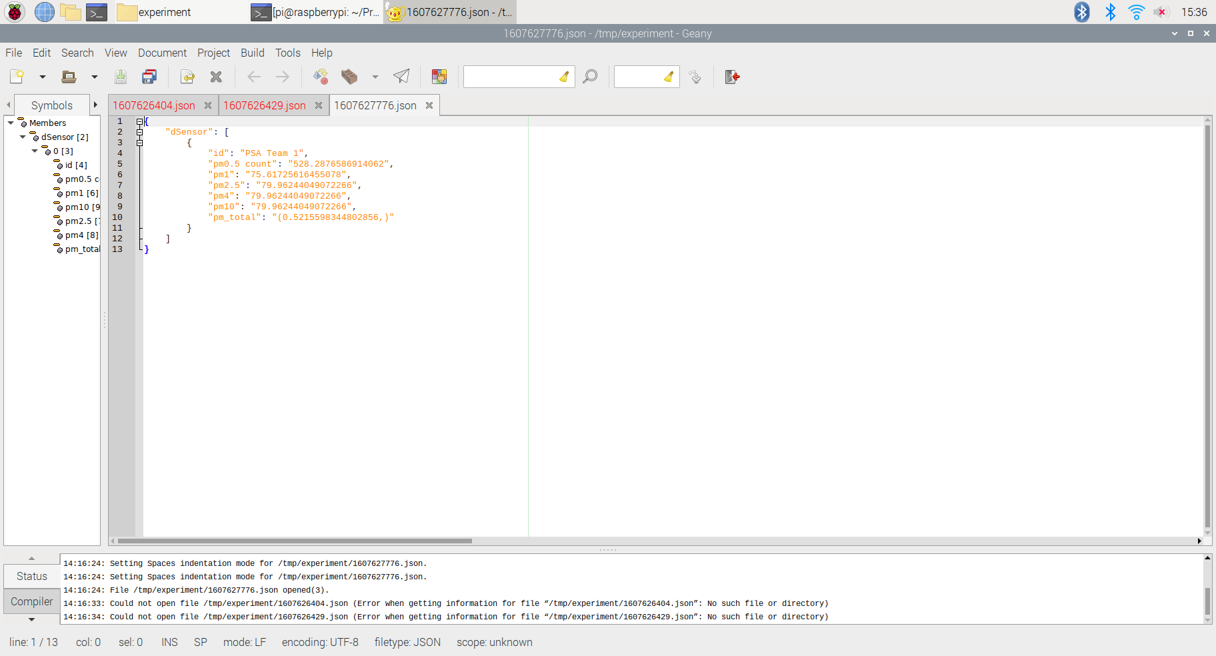
Pictures/lighter_pm_count.png
