mblunt/DETECTS2020/Pictures/normal_air_quality.png

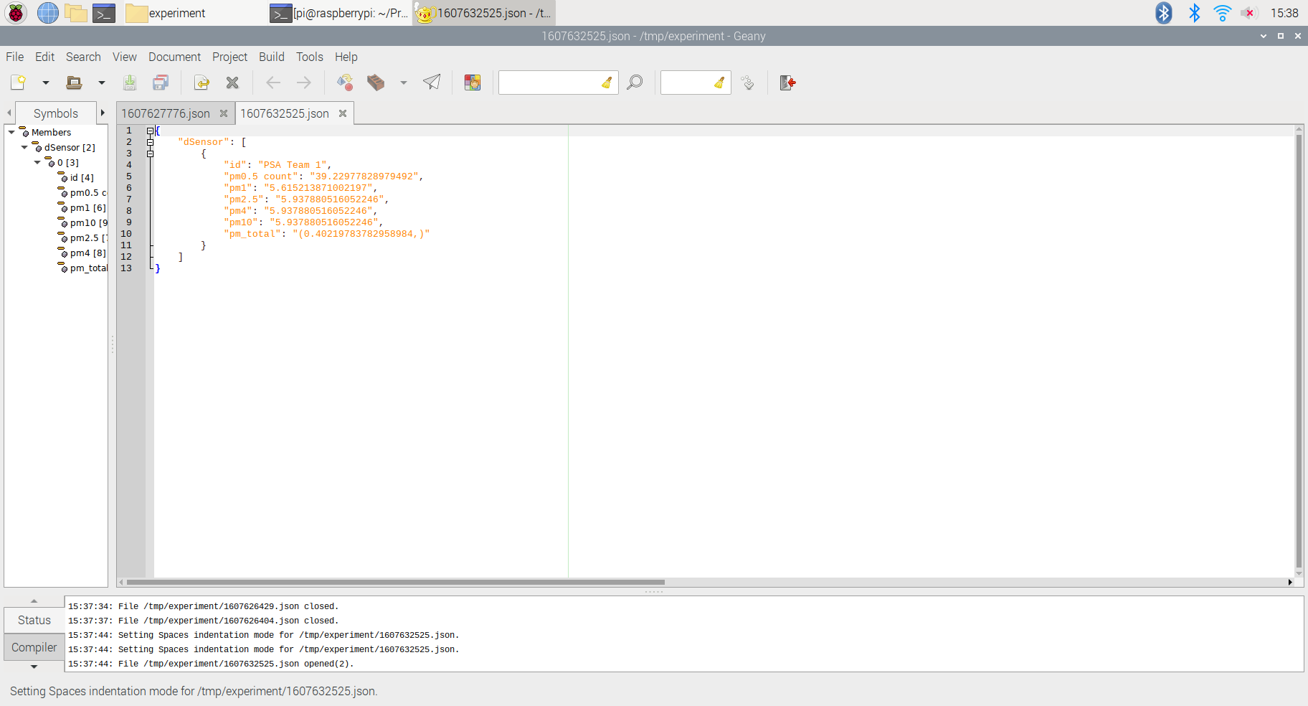
Pictures/normal_air_quality.png
