mblunt/DETECTS2020/Pictures/OutreachContent.PNG

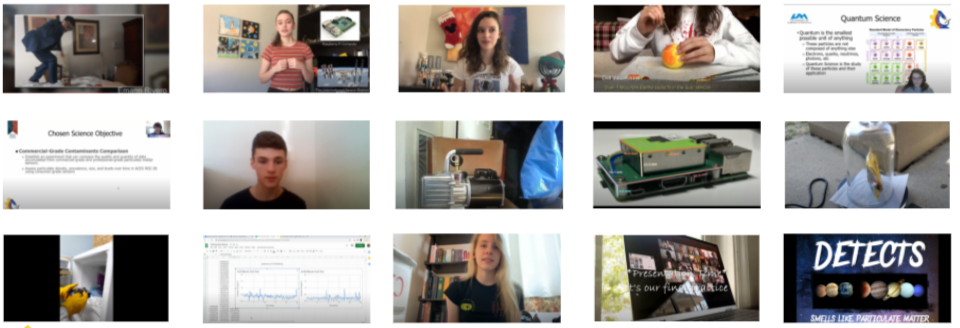
Pictures/OutreachContent.PNG
