mblunt/DETECTS2020/Pictures/page4.jpg

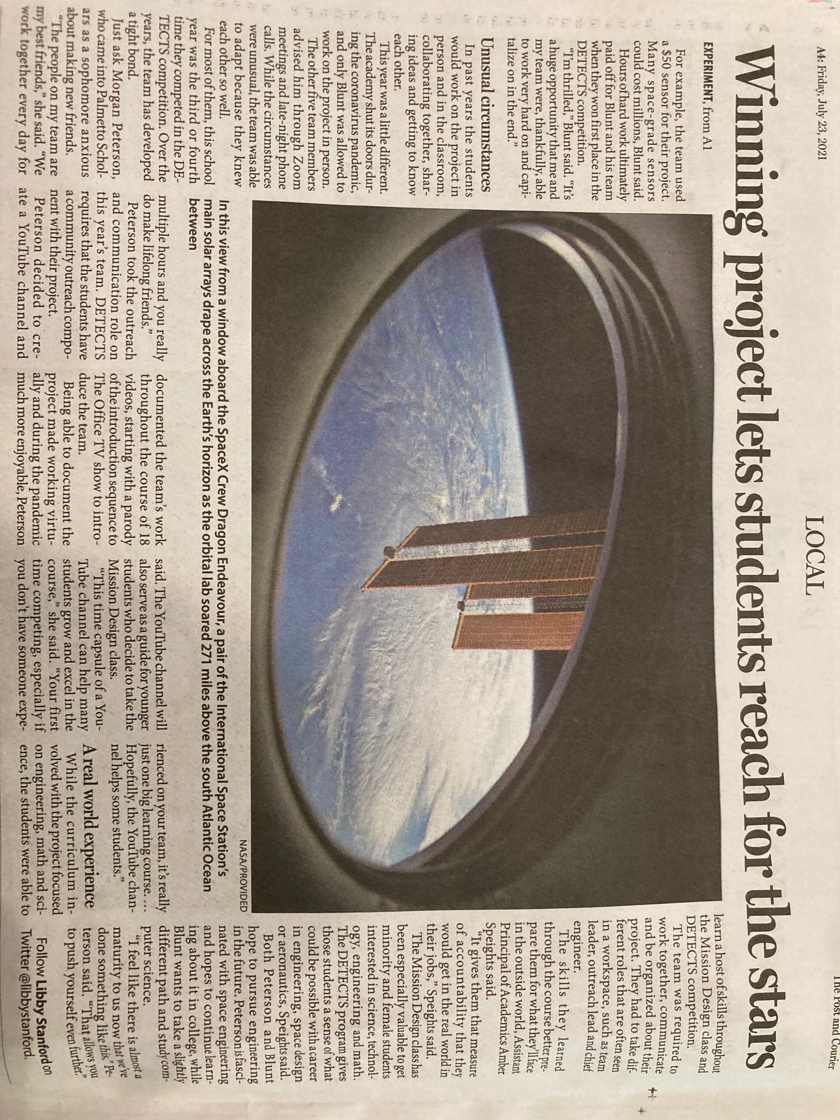
Pictures/page4.jpg
