mblunt/DETECTS2020/Pictures/Payload.jpg

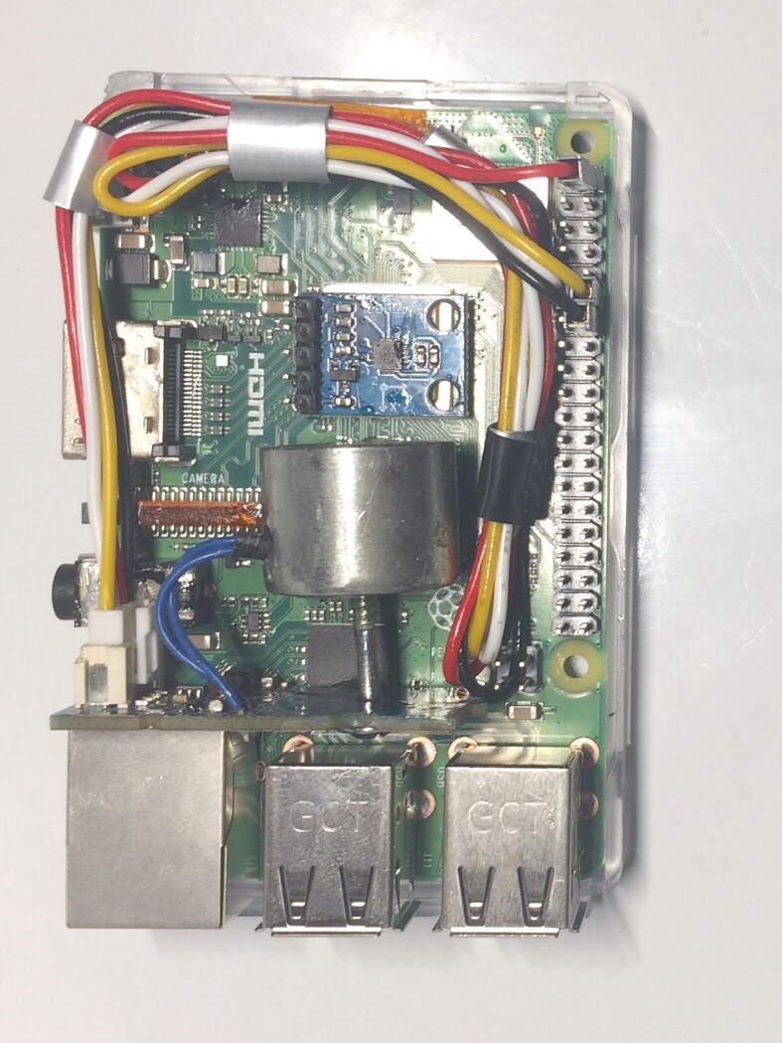
Pictures/Payload.jpg
