mblunt/DETECTS2020/Pictures/PayloadFinalPic1.jpg

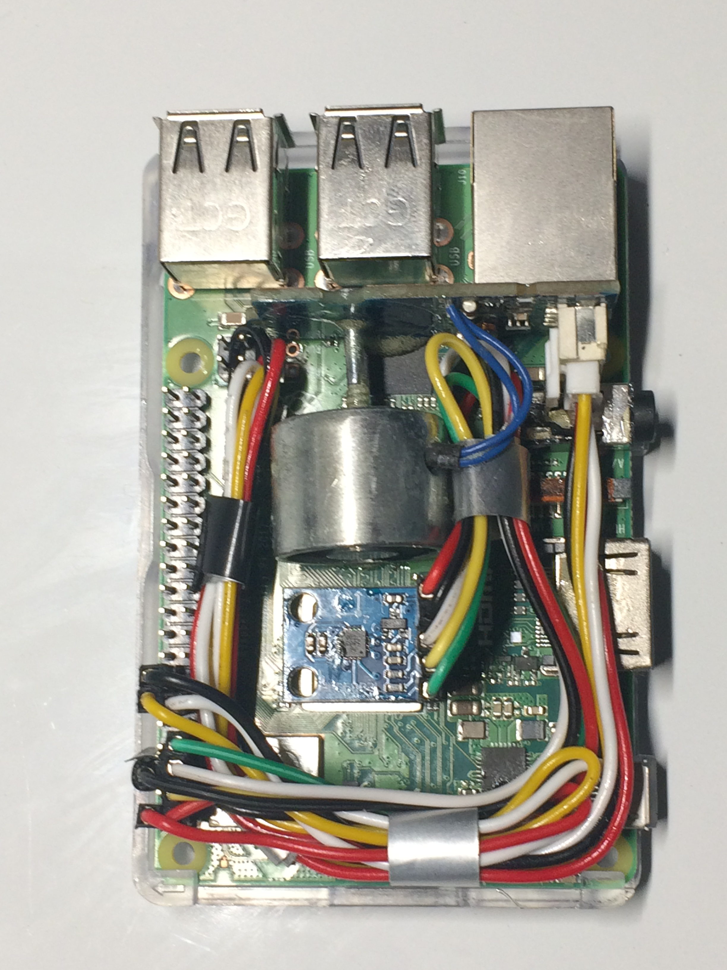
Pictures/PayloadFinalPic1.jpg
