mblunt/DETECTS2020/Pictures/Screenshot1.PNG

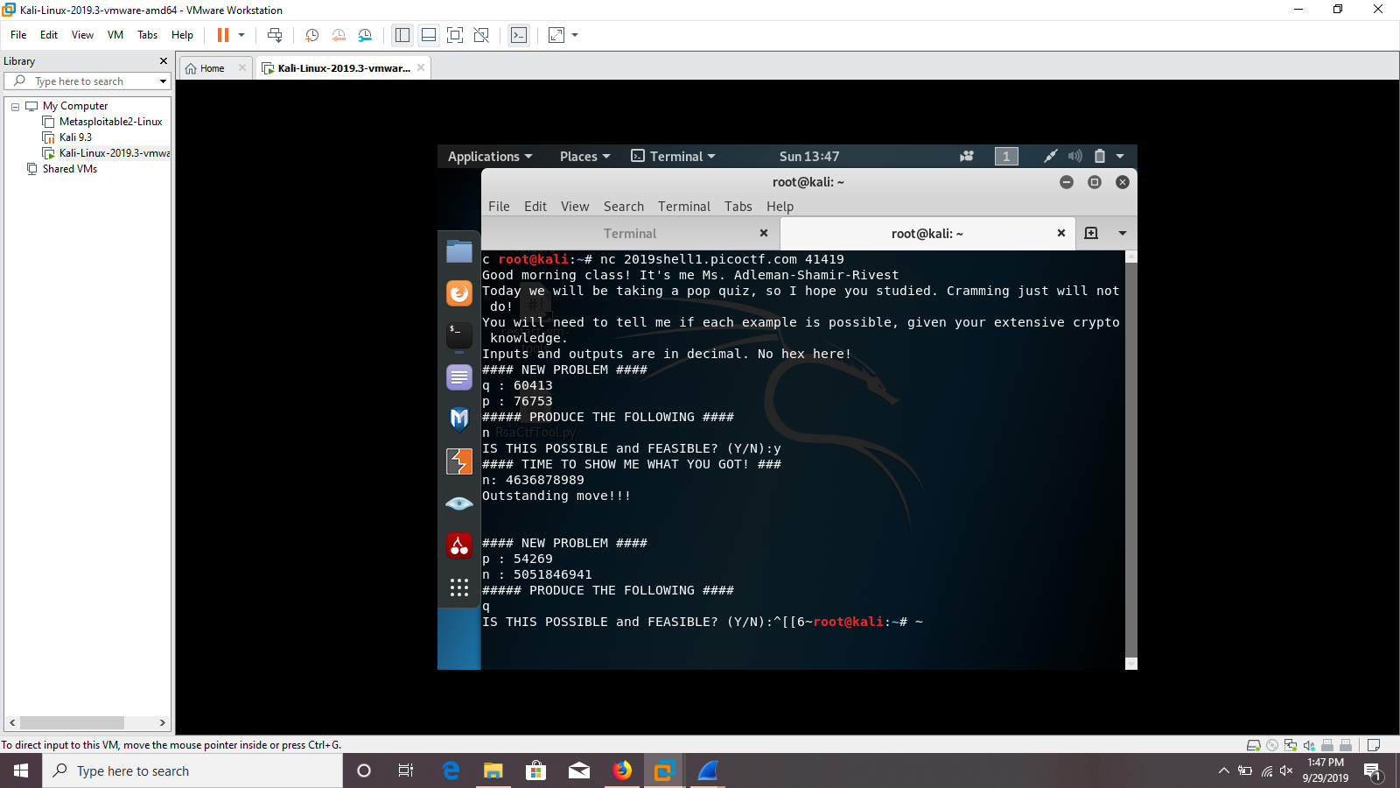
Pictures/Screenshot1.PNG
