mblunt/DETECTS2020/Pictures/SPS30.PNG

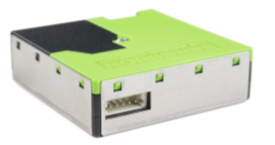
Pictures/SPS30.PNG
