mblunt/DETECTS2020/Pictures/TeamStructureSlide.PNG

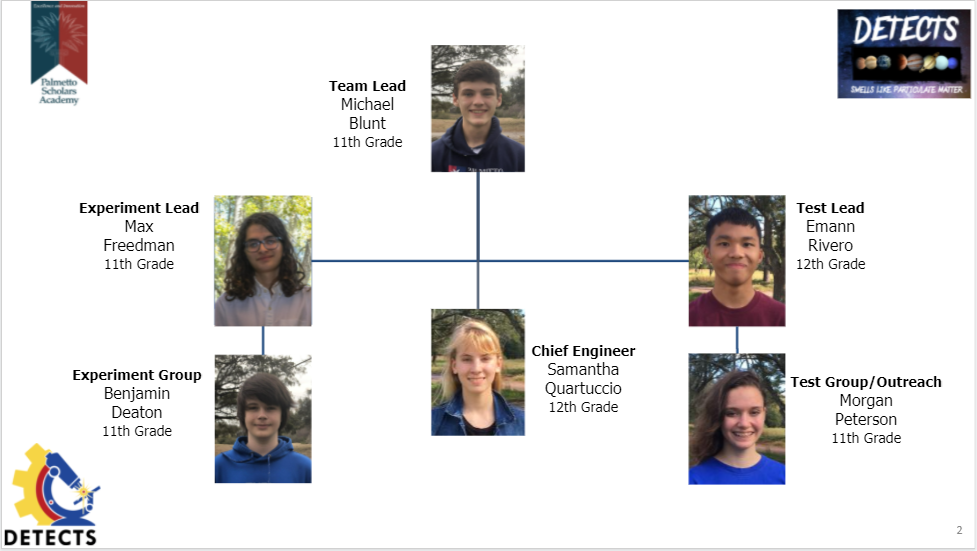
Pictures/TeamStructureSlide.PNG
