mblunt/DETECTS2020/Pictures/transfer1.png

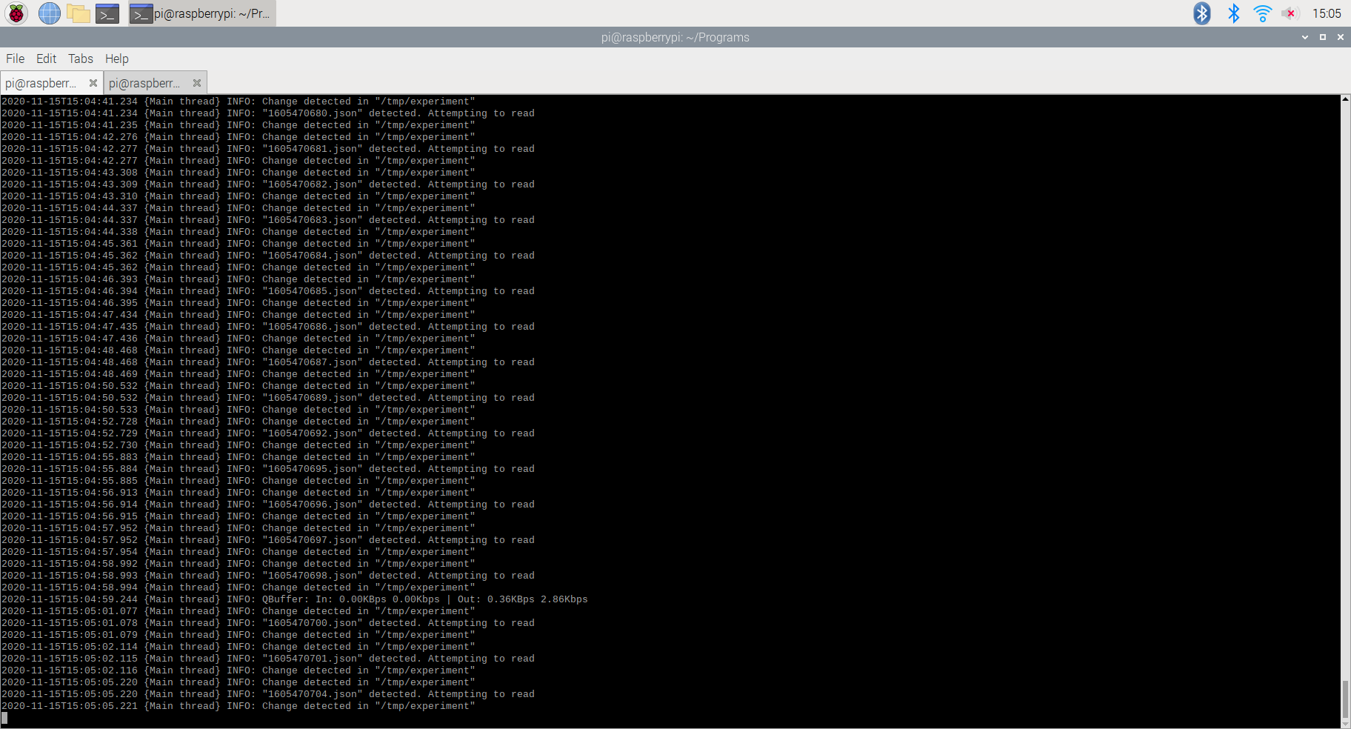
Pictures/transfer1.png
