mblunt/DETECTS2020/Pictures/Untitled drawing (1).png

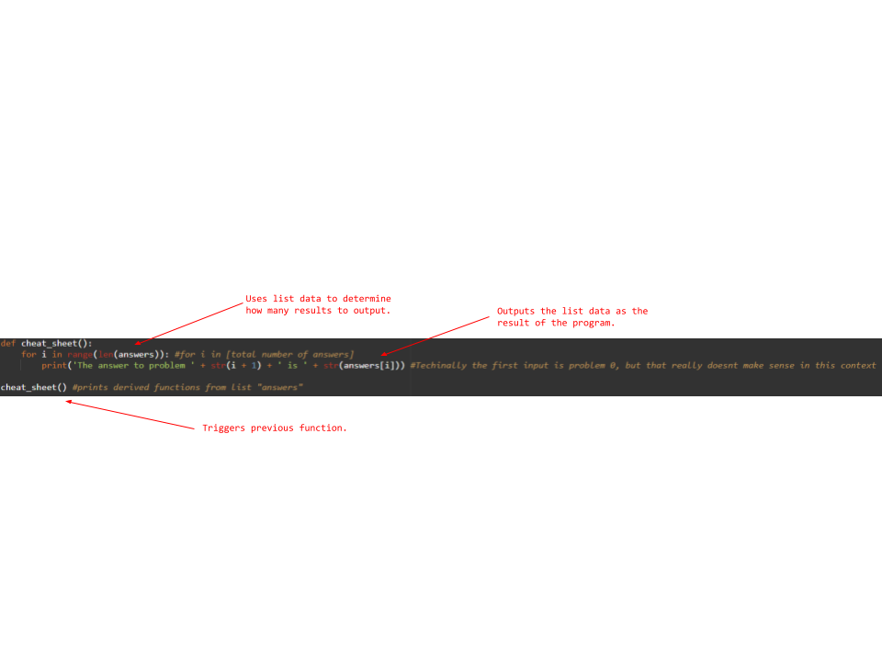
Pictures/Untitled drawing (1).png
