mblunt/DETECTS2020/Pictures/Youtube.PNG

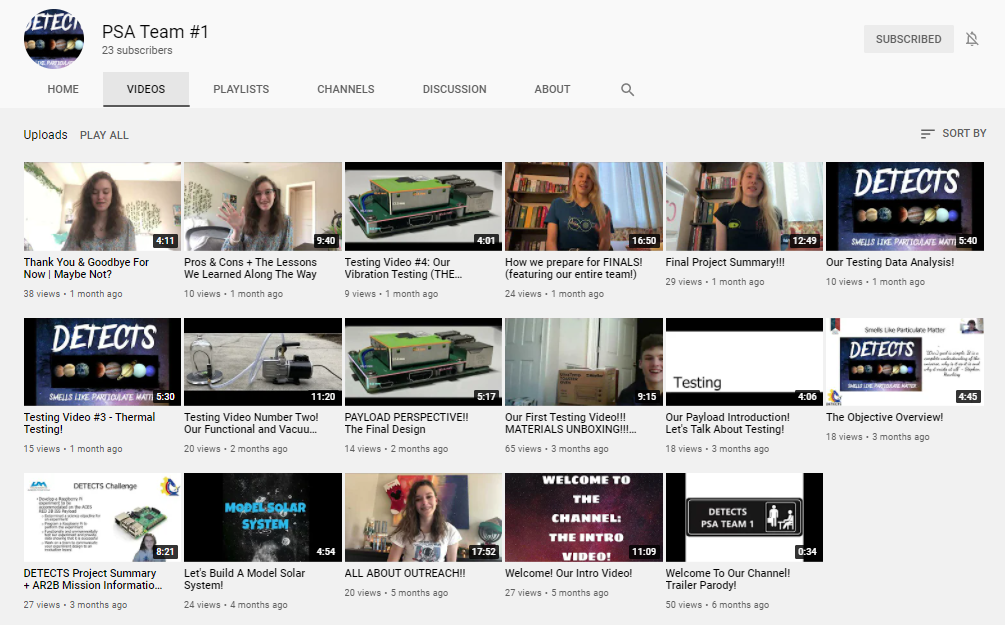
Pictures/Youtube.PNG
