mblunt/DETECTS2020/AR2B_Experiment/Programs/Data_Packet_Info.png

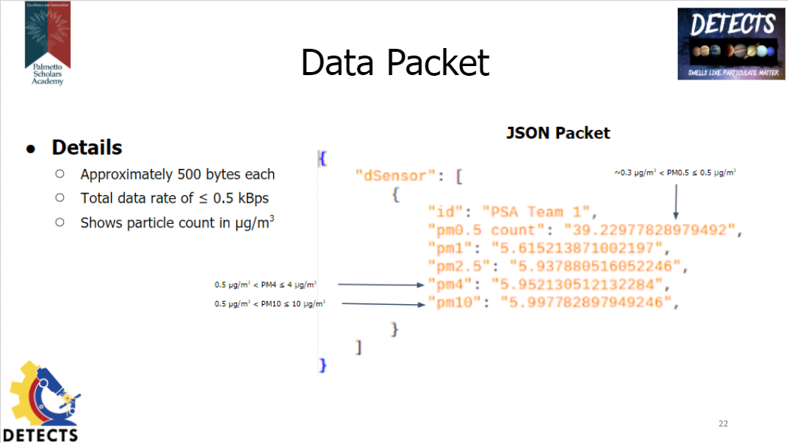
AR2B_Experiment/Programs/Data_Packet_Info.png
