mblunt/DETECTS2020/AR2B_Experiment/Programs/Program_CONOPS.png

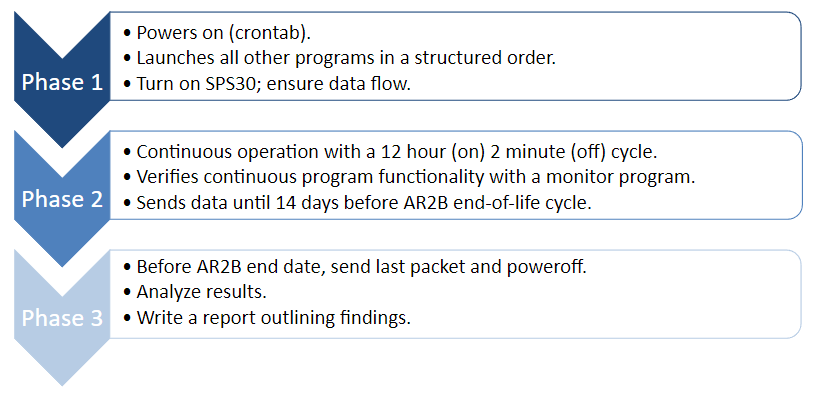
AR2B_Experiment/Programs/Program_CONOPS.png
