mblunt/DETECTS2020/AR2B_Experiment/Programs/Program_Flowchart.png

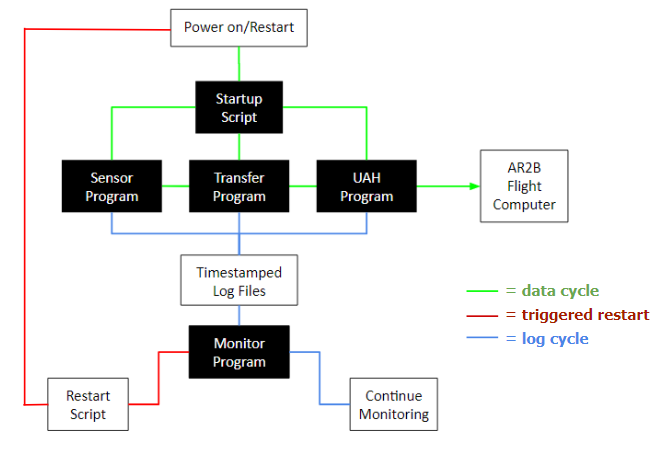
AR2B_Experiment/Programs/Program_Flowchart.png
