mblunt/DETECTS2020/Pictures/BikeTest.png

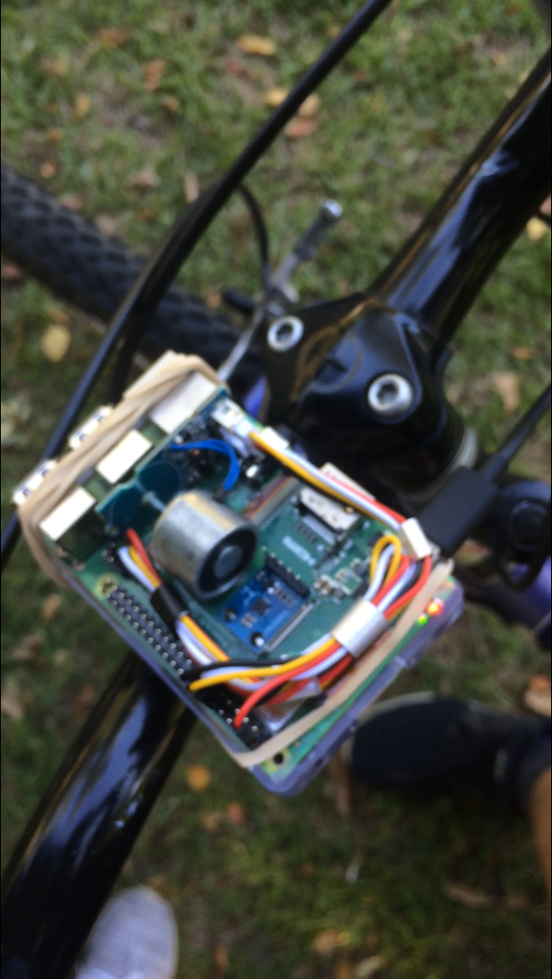
Pictures/BikeTest.png
