mblunt/DETECTS2020/Pictures/populated_tmp_experiment3.png

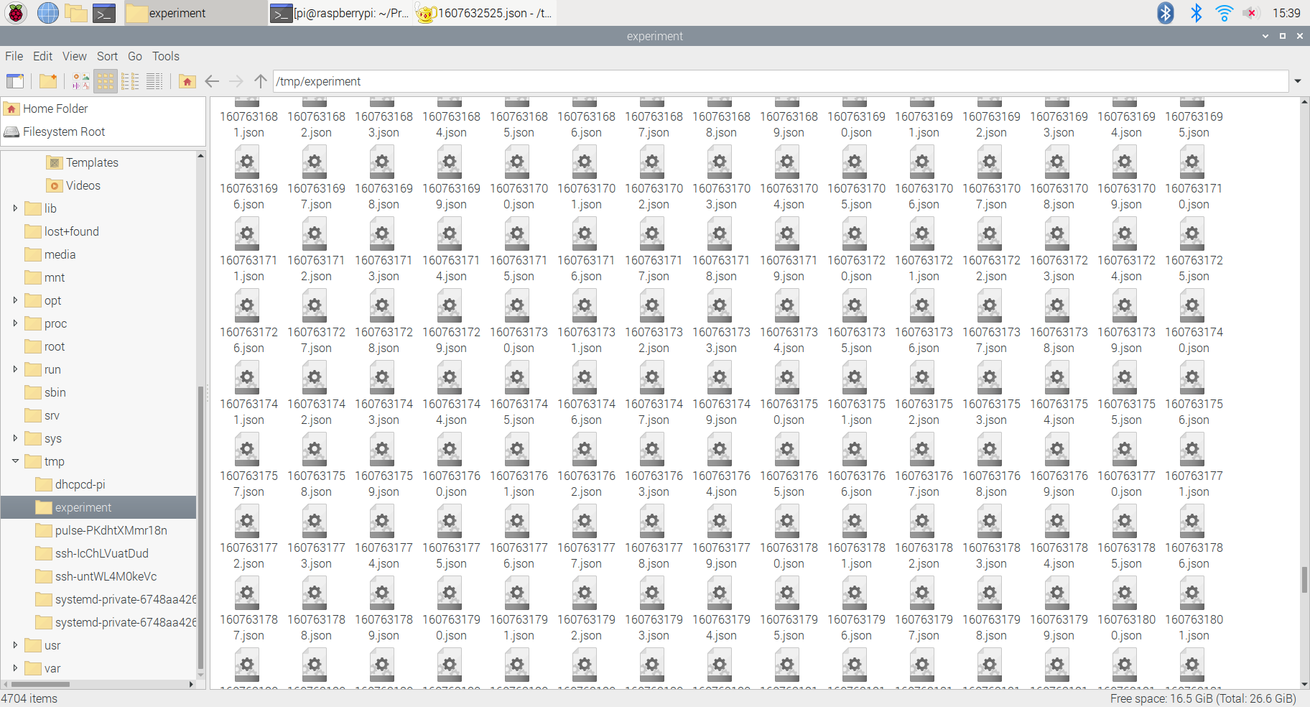
Pictures/populated_tmp_experiment3.png
