mblunt/DETECTS2020/Pictures/populated_tmp_experiment.png

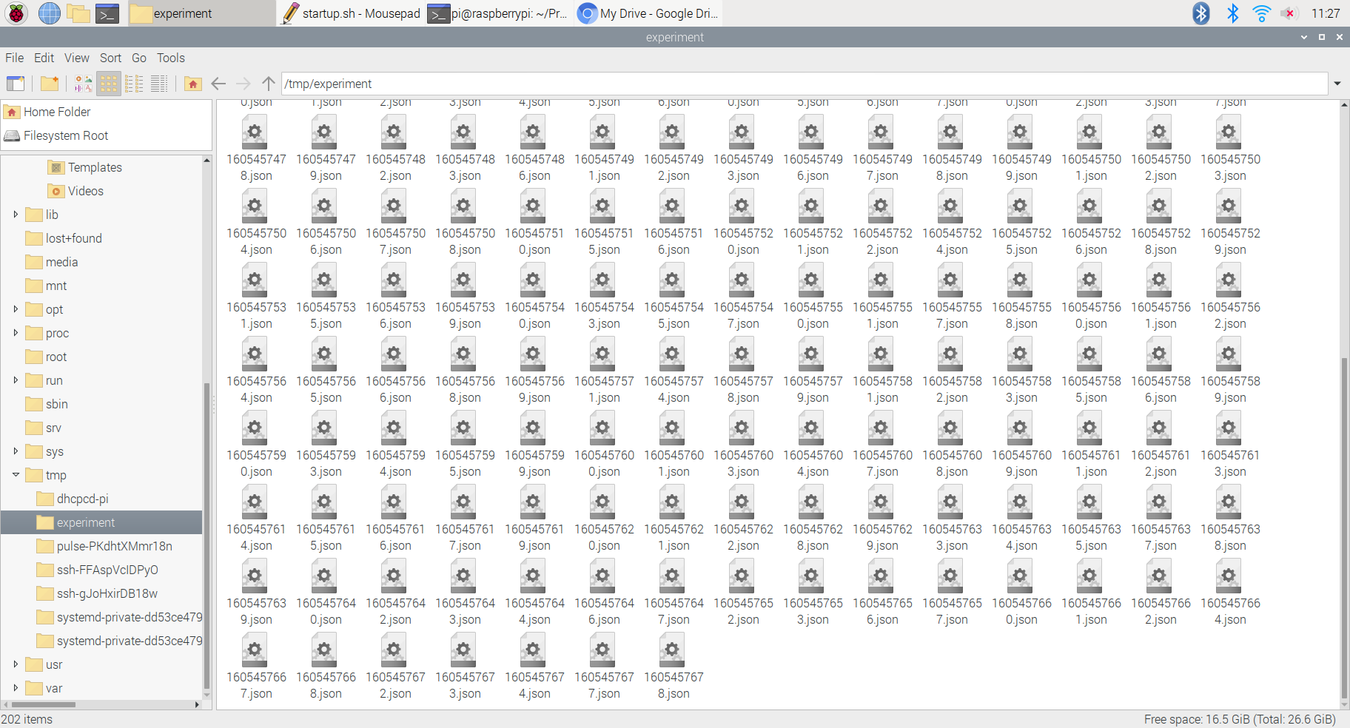
Pictures/populated_tmp_experiment.png
