mblunt/DETECTS2020/Pictures/File_000(2).jpeg

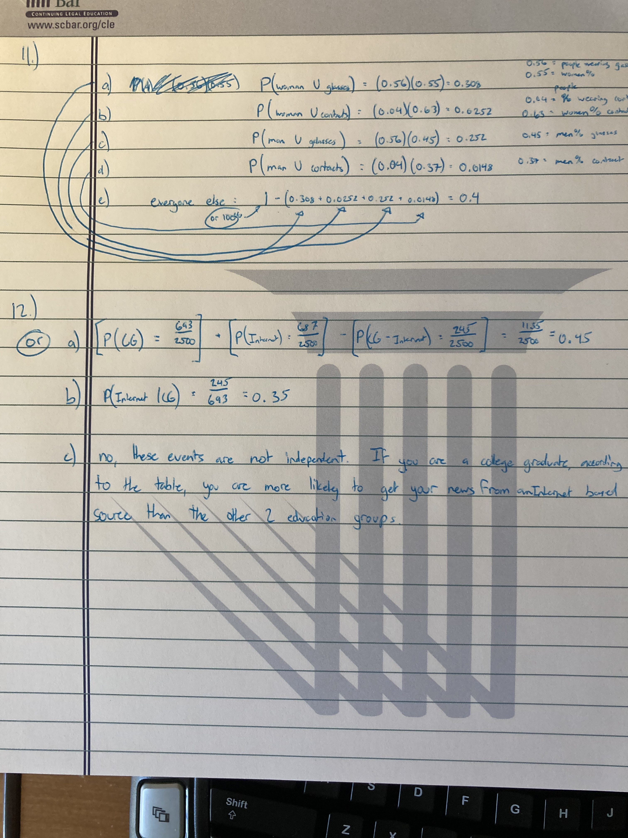
Pictures/File_000(2).jpeg
